AbdulAjadi1/FPGA-Board/documentation/critical_length.png

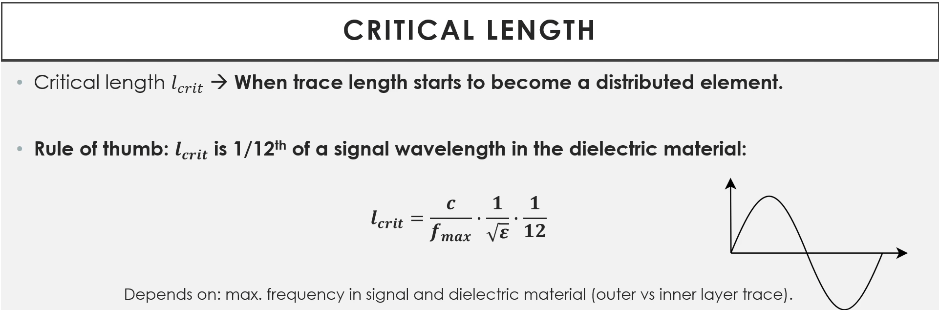
documentation/critical_length.png
