AbdulAjadi1/FPGA-Board/documentation/ddr3.png

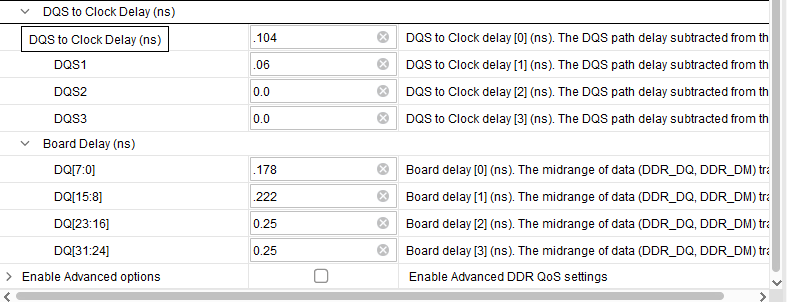
documentation/ddr3.png
