AbdulAjadi1/FPGA-Board/documentation/microstrip_stripline_delay.png

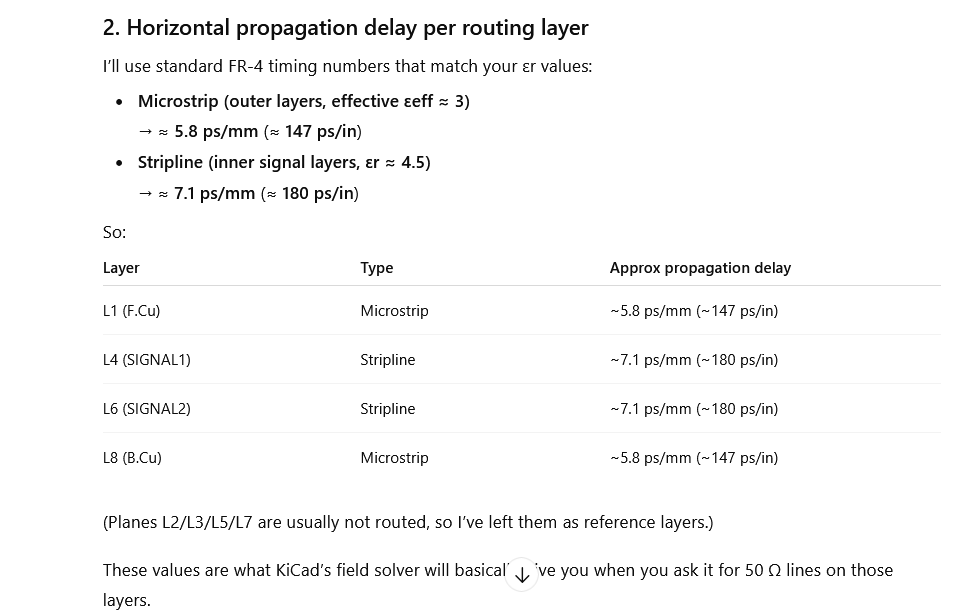
documentation/microstrip_stripline_delay.png
