AbdulAjadi1/FPGA-Board/3dmodels/ECS-2520MV-120-BN-TR.step

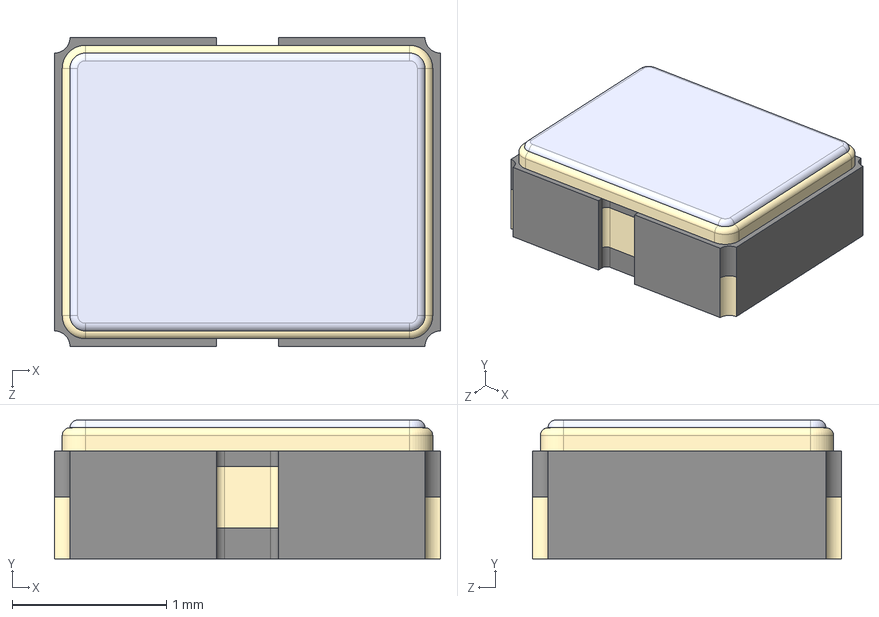
[picture p25: CAD file, 2025-12-17]
3dmodels/ECS-2520MV-120-BN-TR.step
2.50 x 0.9 x 2.00 mm
