AbdulAjadi1/FPGA-Board/3dmodels/cg0402mlu.stp

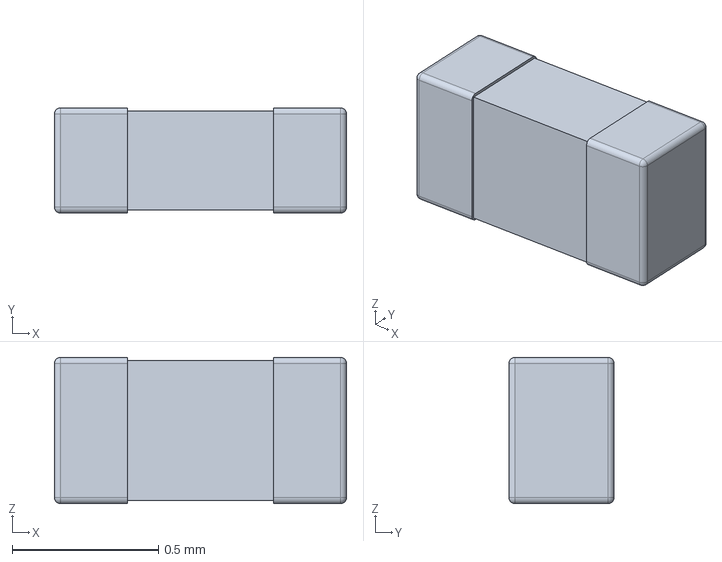
[picture p26: CAD file, 2025-12-17]
3dmodels/cg0402mlu.stp
1.00 x 0.36 x 0.5 mm
