AbdulAjadi1/FPGA-Board/3dmodels/DCU0008A.stp

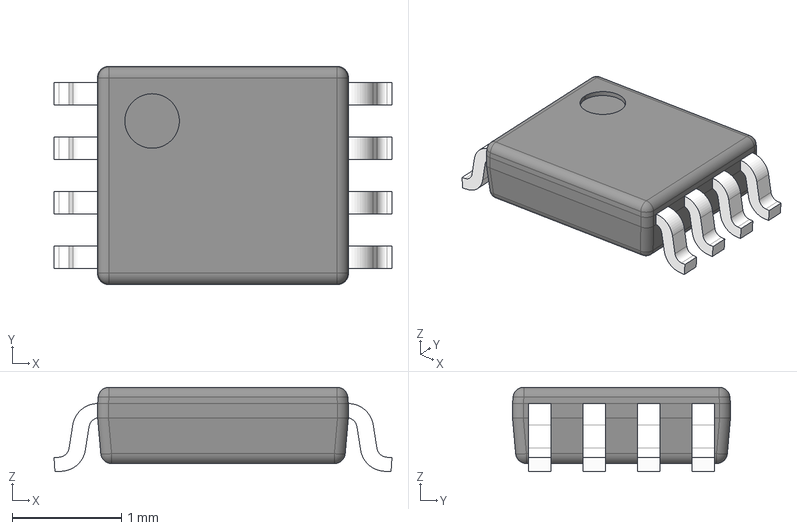
[picture p28: CAD file, 2025-11-05]
3dmodels/DCU0008A.stp
3.10 x 2.00 x 0.775 mm
BODY-VSSOP
LEAD-VSSOP x 8
