AbdulAjadi1/FPGA-Board/3dmodels/R_0201_0603Metric.step

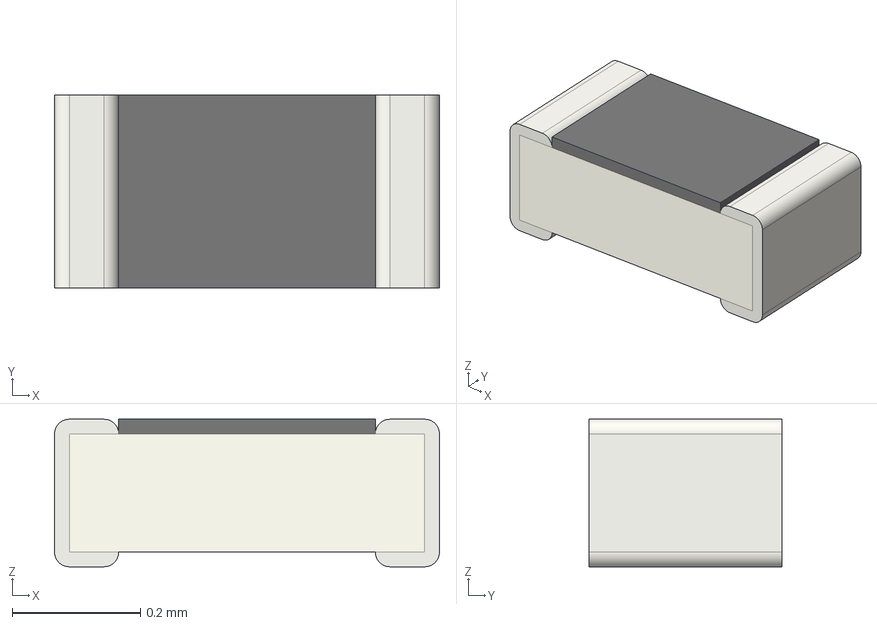
[picture p29: CAD file, 2025-11-05]
3dmodels/R_0201_0603Metric.step
0.6 x 0.3 x 0.23 mm
