AbdulAjadi1/FPGA-Board/3dmodels/UE27AC54100.step

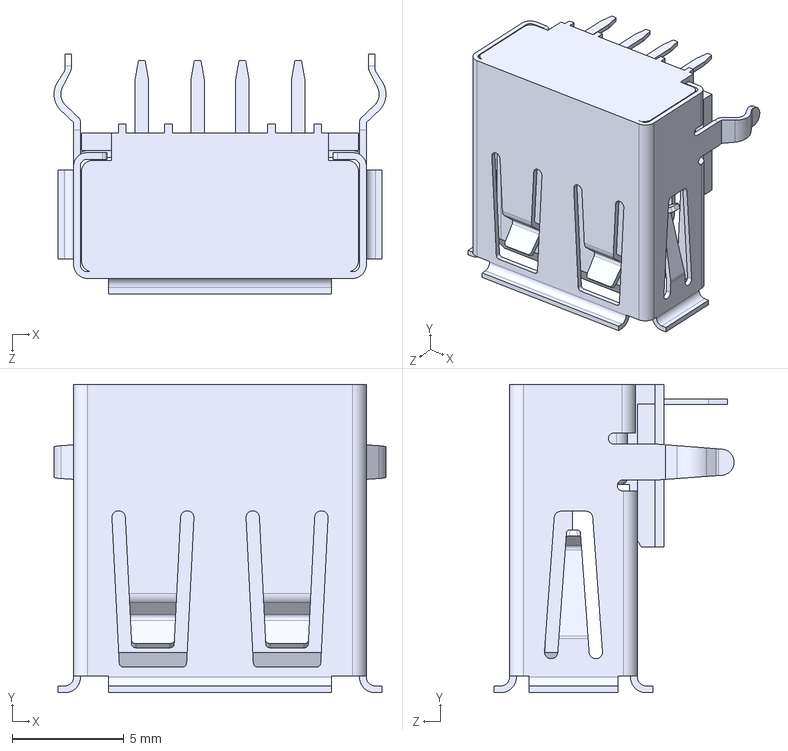
[picture p31: CAD file, 2025-09-09]
3dmodels/UE27AC54100.step
14.9 x 13.8 x 10.7 mm
