AbdulAjadi1/FPGA-Board/3dmodels/PJ-102AH.STEP

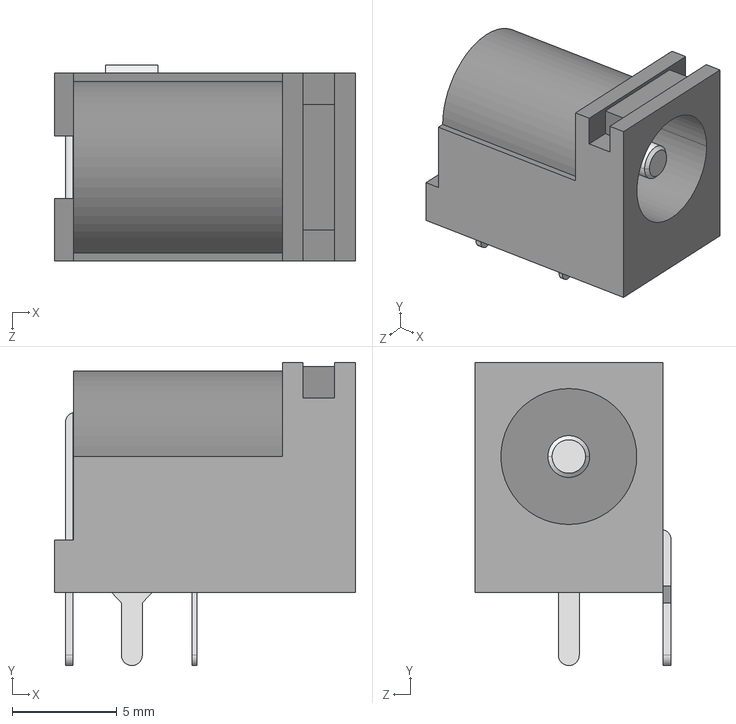
[picture p32: CAD file, 2025-09-09]
3dmodels/PJ-102AH.STEP
14.4 x 14.5 x 9.40 mm
