AbdulAjadi1/FPGA-Board/3dmodels/CR_050R3C2P_AVX.step

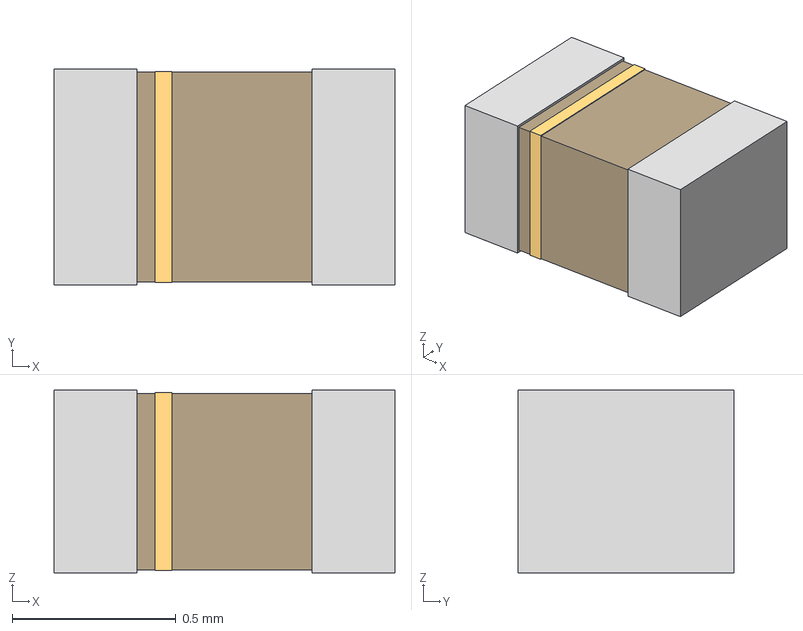
[picture p33: CAD file, 2025-09-09]
3dmodels/CR_050R3C2P_AVX.step
1.04 x 0.66 x 0.559 mm
