AbdulAjadi1/FPGA-Board/3dmodels/SJ1-3525NG.STEP

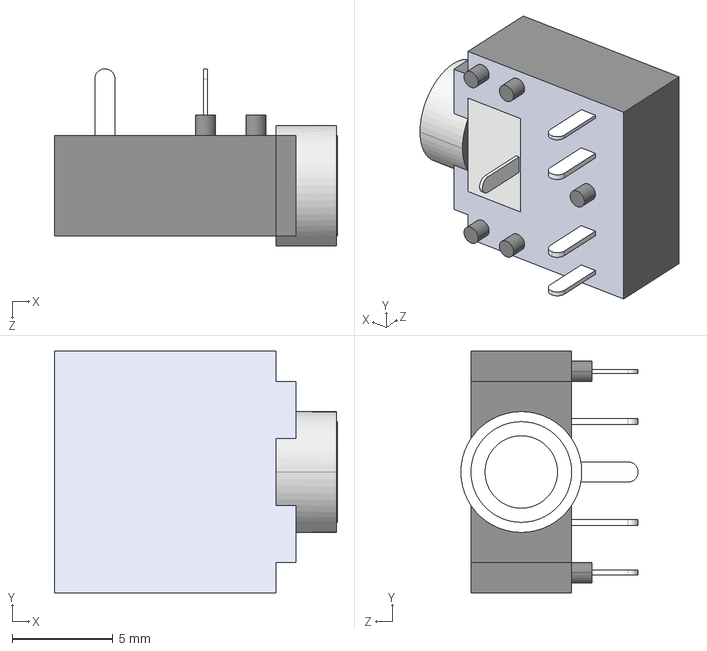
[picture p34: CAD file, 2025-09-09]
3dmodels/SJ1-3525NG.STEP
14.0 x 12.0 x 8.80 mm
