AbdulAjadi1/FPGA-Board/3dmodels/RM_10_ADI.step

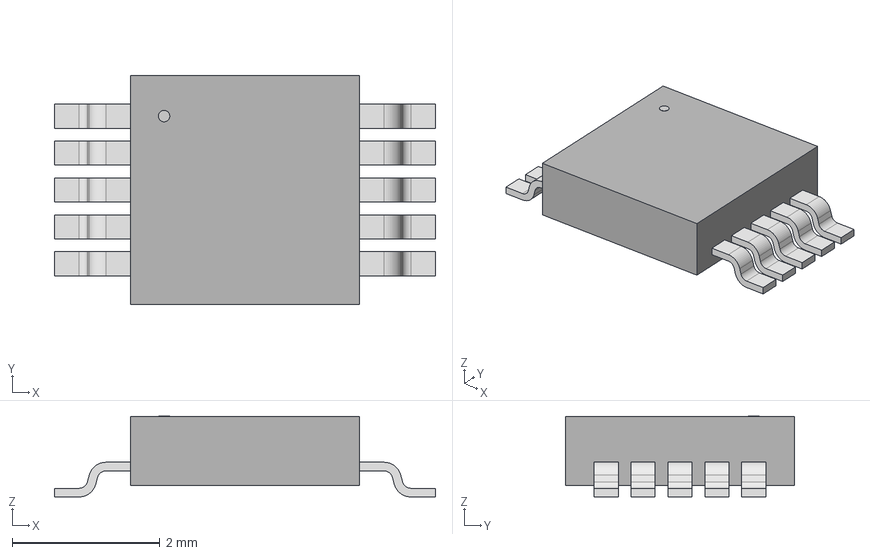
[picture p35: CAD file, 2025-09-09]
3dmodels/RM_10_ADI.step
5.16 x 3.10 x 1.09 mm
