AbdulAjadi1/FPGA-Board/3dmodels/TSX-322526_0000MF09Z-AC3_EPS.step

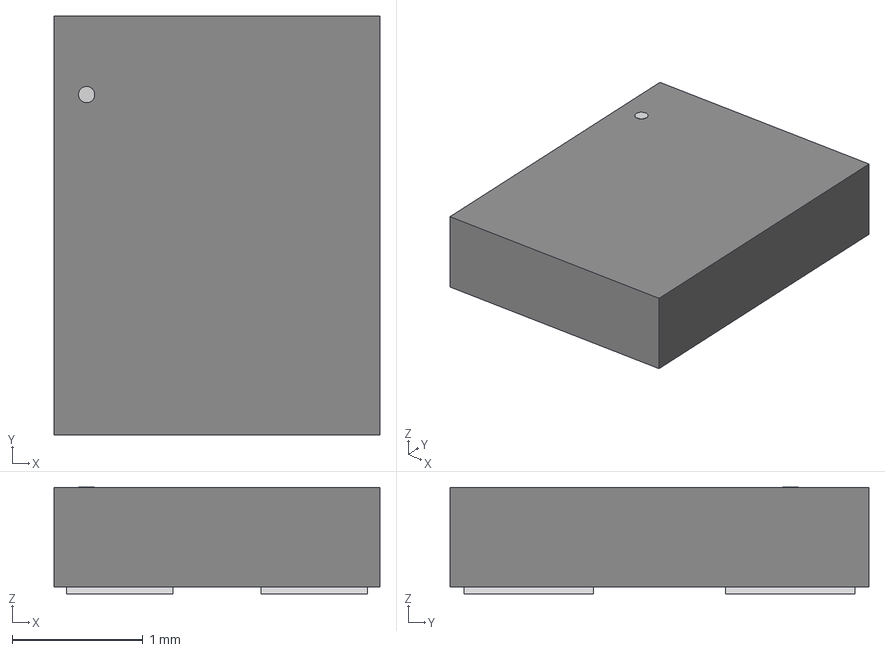
[picture p36: CAD file, 2025-09-09]
3dmodels/TSX-322526_0000MF09Z-AC3_EPS.step
2.49 x 3.20 x 0.815 mm
