AbdulAjadi1/FPGA-Board/3dmodels/NR5040T2R2N.STEP

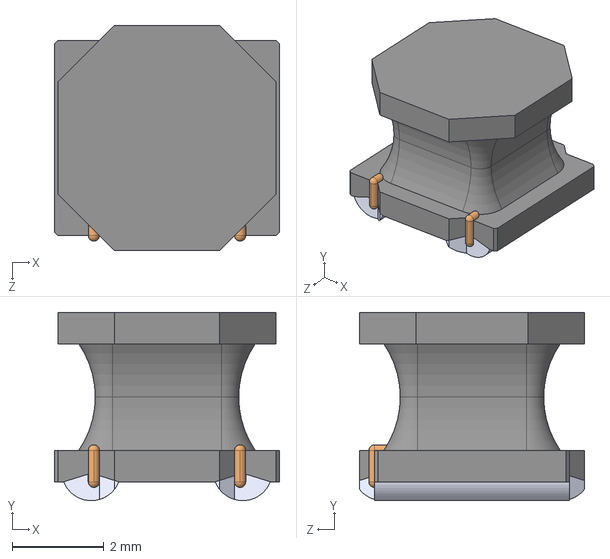
[picture p38: CAD file, 2025-09-09]
3dmodels/NR5040T2R2N.STEP
4.90 x 4.10 x 4.90 mm
