AbdulAjadi1/FPGA-Board/3dmodels/BAS16XV2T1G.step

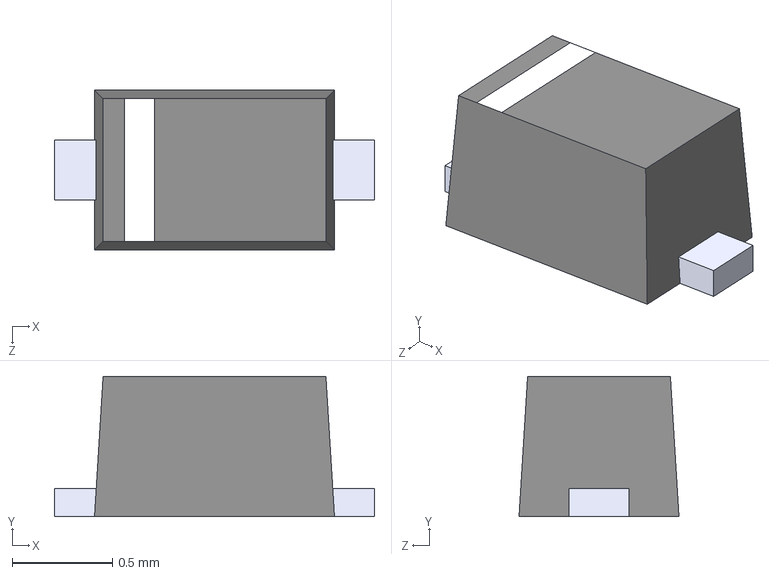
[picture p40: CAD file, 2025-09-09]
3dmodels/BAS16XV2T1G.step
1.60 x 0.7 x 0.8 mm
