AbdulAjadi1/FPGA-Board/3dmodels/DBV0006A.stp

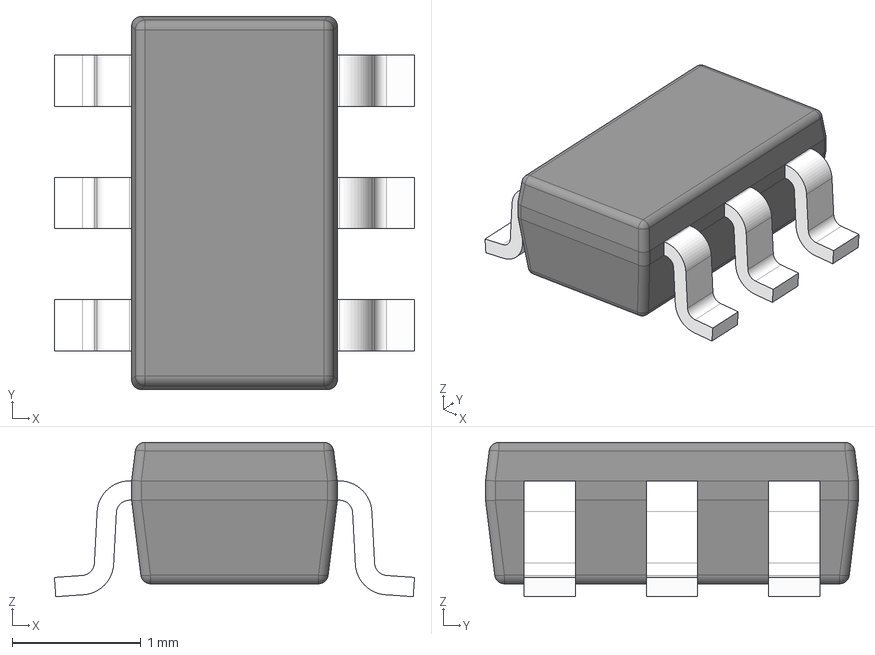
[picture p41: CAD file, 2025-09-09]
3dmodels/DBV0006A.stp
2.80 x 2.90 x 1.20 mm
BODY-SOT
LEAD-SOT x 6
