AbdulAjadi1/FPGA-Board/3dmodels/EG1218.step

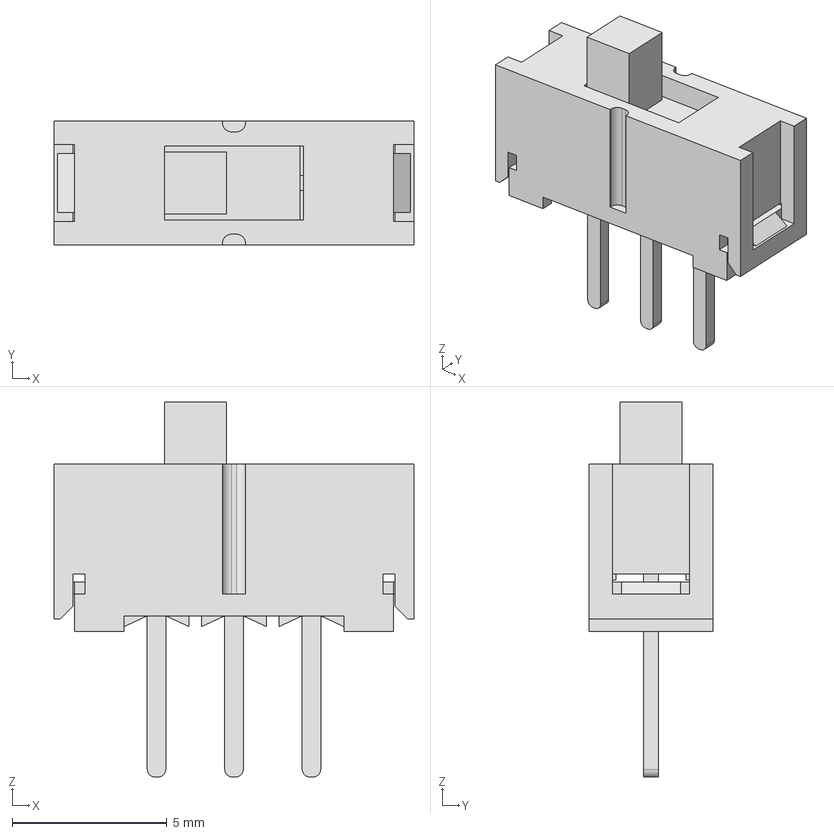
[picture p42: CAD file, 2025-09-09]
3dmodels/EG1218.step
11.6 x 4.00 x 12.1 mm
