AbdulAjadi1/FPGA-Board/3dmodels/c-5787834-1-c-3d.stp

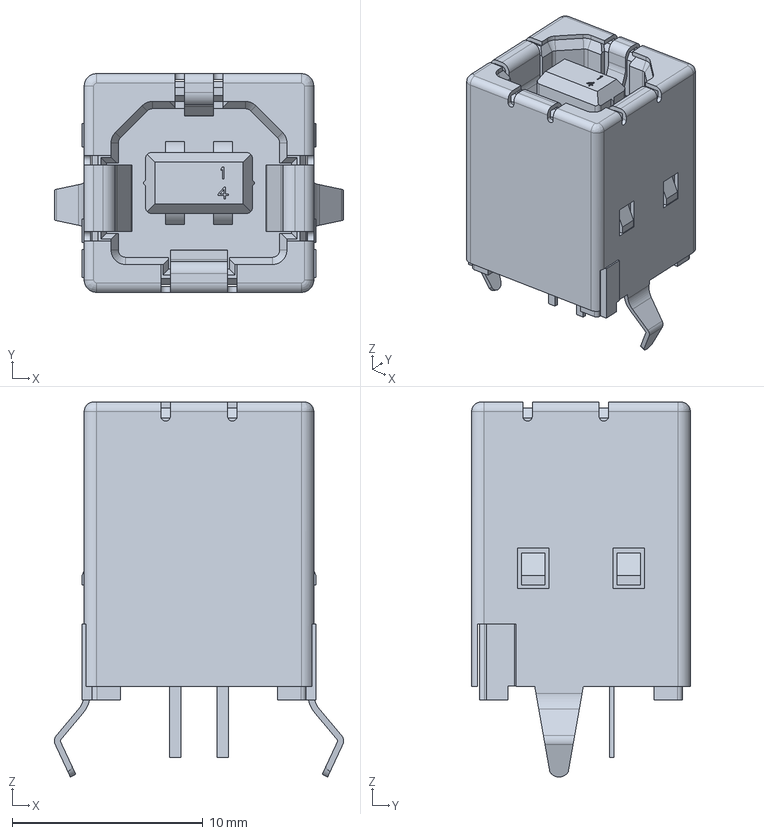
[picture p43: CAD file, 2025-09-09]
3dmodels/c-5787834-1-c-3d.stp
15.1 x 11.5 x 19.6 mm
