AbdulAjadi1/FPGA-Board/3dmodels/IND_TYS60282_LRD.step

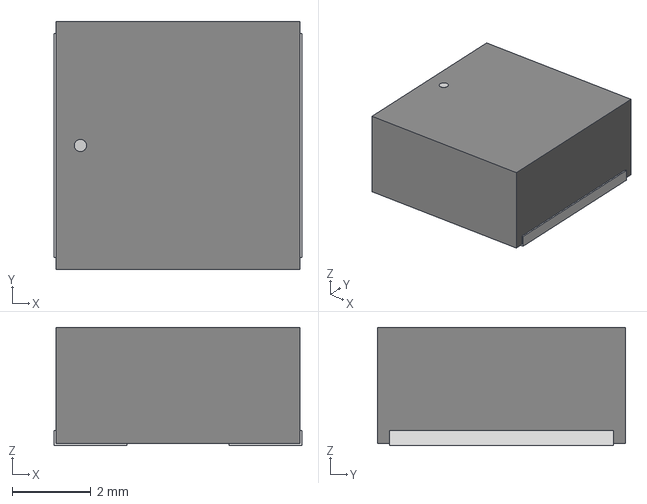
[picture p44: CAD file, 2025-09-09]
3dmodels/IND_TYS60282_LRD.step
6.30 x 6.30 x 3.00 mm
