AbdulAjadi1/FPGA-Board/3dmodels/USB-A-S-F-B-SM2.stp

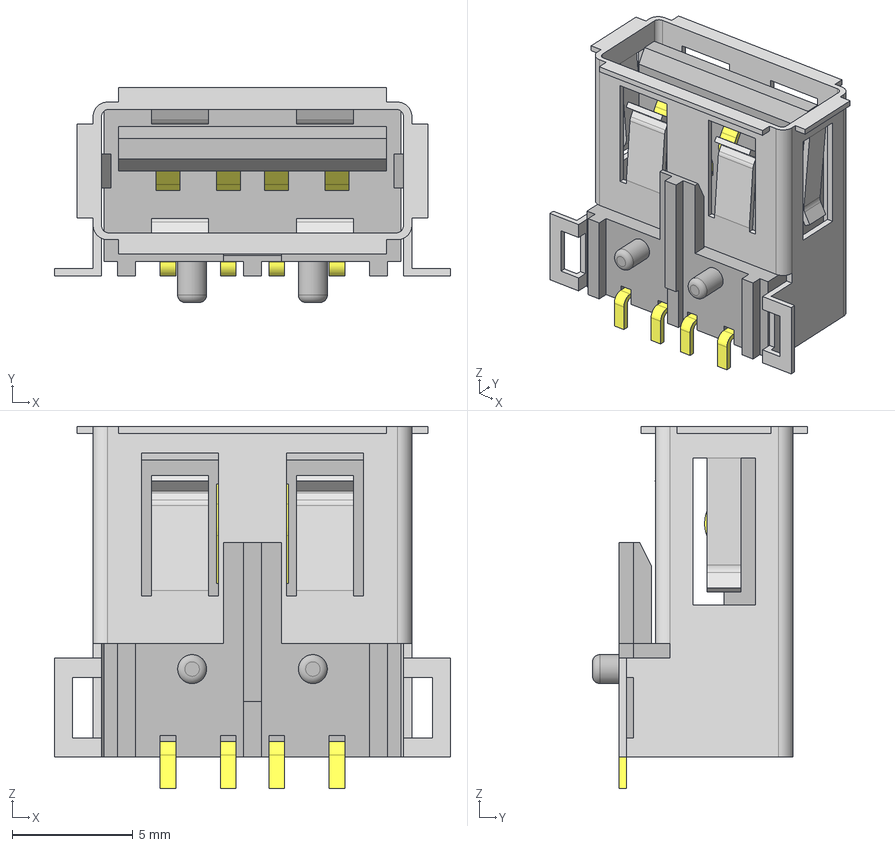
[picture p45: CAD file, 2025-09-09]
3dmodels/USB-A-S-F-B-SM2.stp
16.4 x 8.90 x 15.0 mm
USB-A-S-SM2_S
USB-A-S-B-SM2_B
USB-A-S-SM2_P
