AbdulAjadi1/FPGA-Board/3dmodels/BSS214NH6327XTSA1.stp

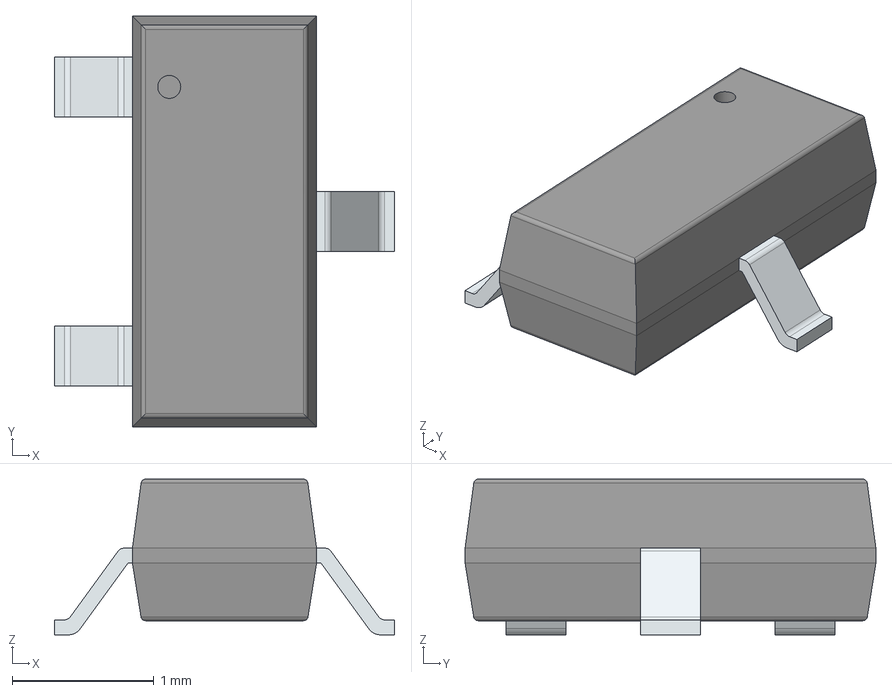
[picture p46: CAD file, 2025-09-09]
3dmodels/BSS214NH6327XTSA1.stp
2.40 x 2.90 x 1.10 mm
PinsArrayL
FilletPinR
