AbdulAjadi1/FPGA-Board/3dmodels/SO3016_INF.step

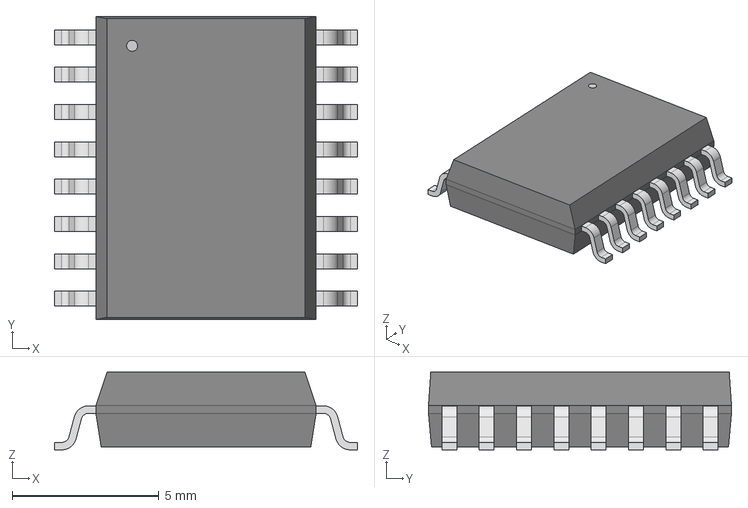
[picture p47: CAD file, 2025-09-09]
3dmodels/SO3016_INF.step
10.3 x 10.3 x 2.64 mm
