AbdulAjadi1/FPGA-Board/3dmodels/LED_0402_1005Metric.step

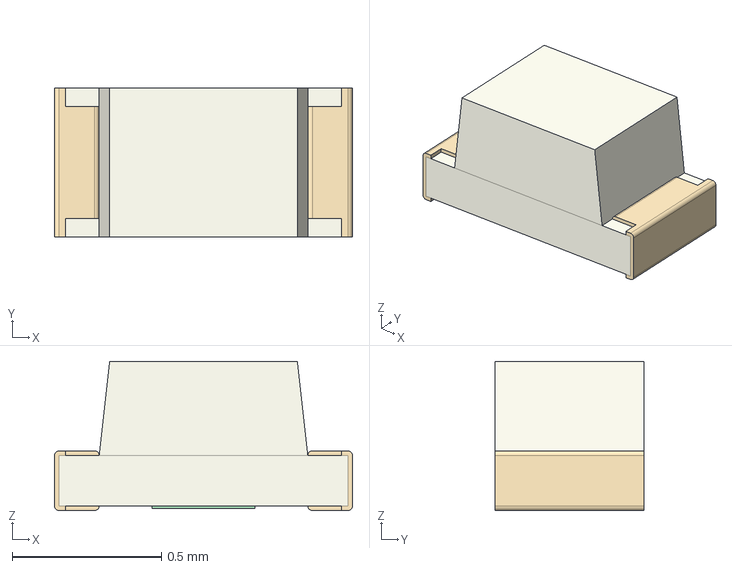
[picture p48: CAD file, 2025-09-09]
3dmodels/LED_0402_1005Metric.step
1.00 x 0.5 x 0.5 mm
