AbdulAjadi1/FPGA-Board/3dmodels/NL17SZ17XV5T2G.STEP

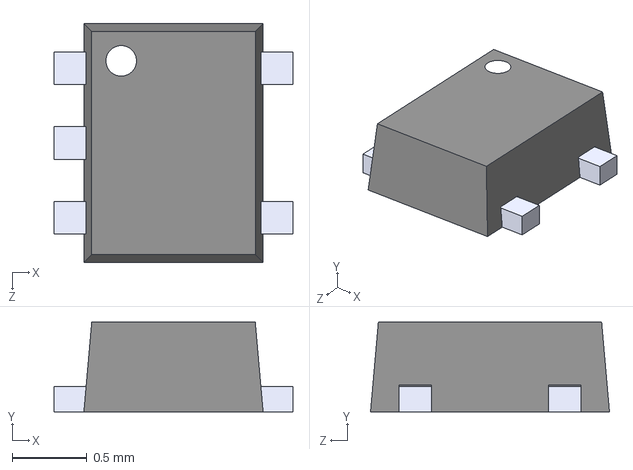
[picture p49: CAD file, 2025-09-09]
3dmodels/NL17SZ17XV5T2G.STEP
1.60 x 0.6 x 1.60 mm
