AbdulAjadi1/FPGA-Board/3dmodels/LED_SMLV56_ROM.step

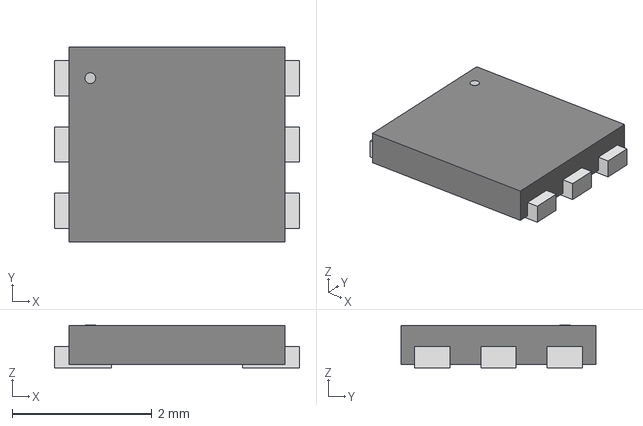
[picture p50: CAD file, 2025-09-09]
3dmodels/LED_SMLV56_ROM.step
3.51 x 2.79 x 0.612 mm
