AbdulAjadi1/FPGA-Board/3dmodels/IS43TR16256B-125KBLI.step

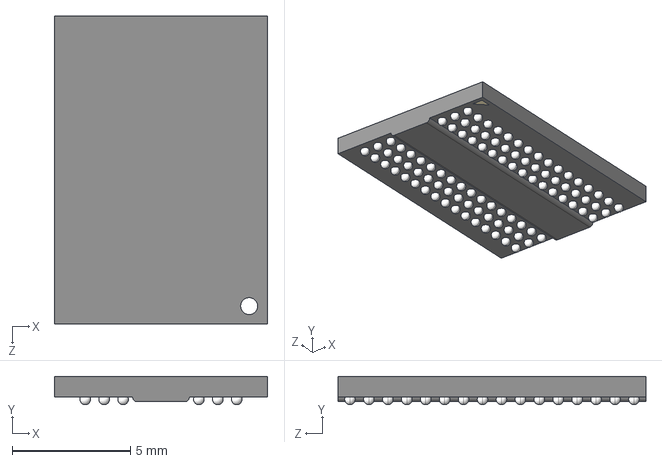
[picture p51: CAD file, 2025-09-09]
3dmodels/IS43TR16256B-125KBLI.step
9.00 x 1.20 x 13.0 mm
