AbdulAjadi1/FPGA-Board/3dmodels/DBZ0003A.stp

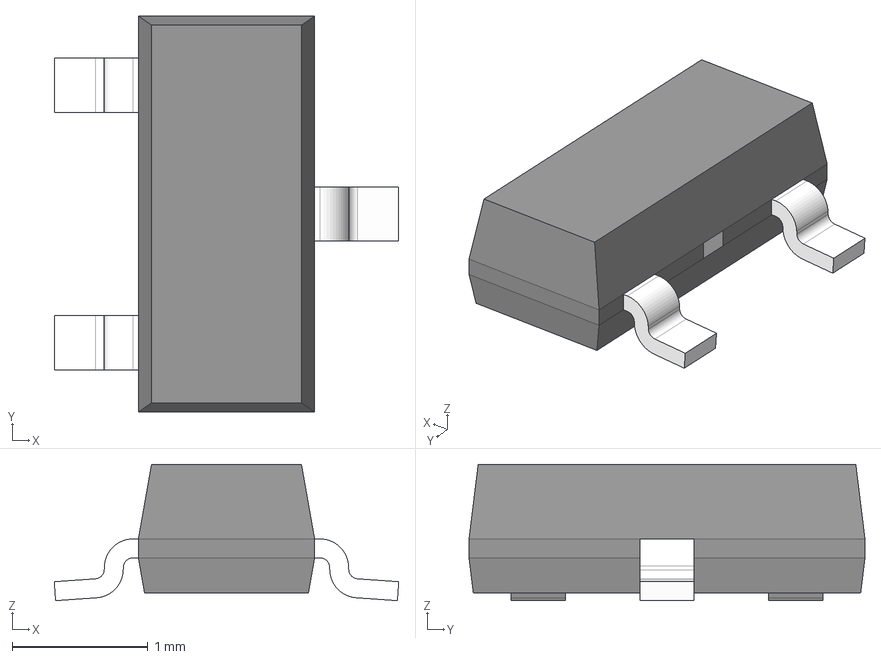
[picture p52: CAD file, 2025-09-09]
3dmodels/DBZ0003A.stp
2.54 x 2.92 x 1.01 mm
BODY-SOT
LEAD-SOT x 3
PIN1-ID
TIEBAR
