AbdulAjadi1/FPGA-Board/3dmodels/ABMM-25.000MHZ-B2-T.step

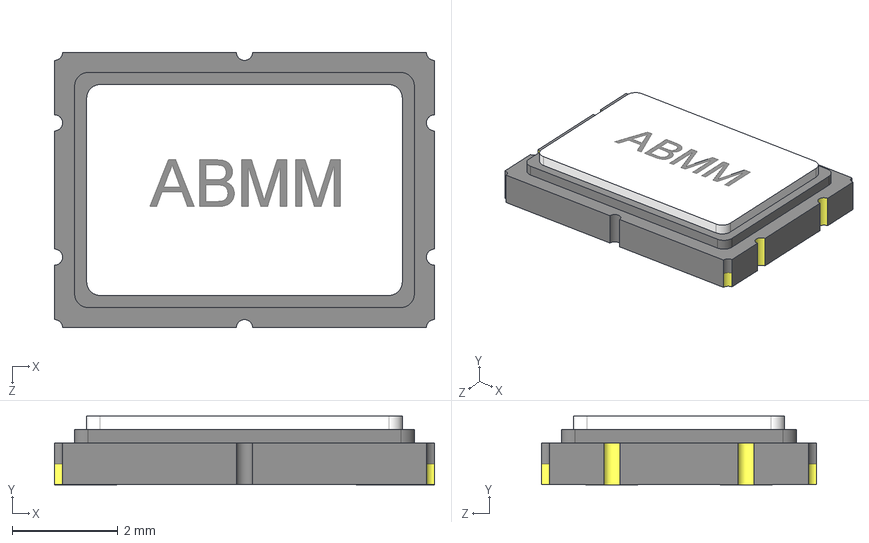
[picture p53: CAD file, 2025-09-09]
3dmodels/ABMM-25.000MHZ-B2-T.step
7.19 x 1.30 x 5.21 mm
