AbdulAjadi1/FPGA-Board/3dmodels/PinHeader_1x02_P2.54mm_Vertical.step

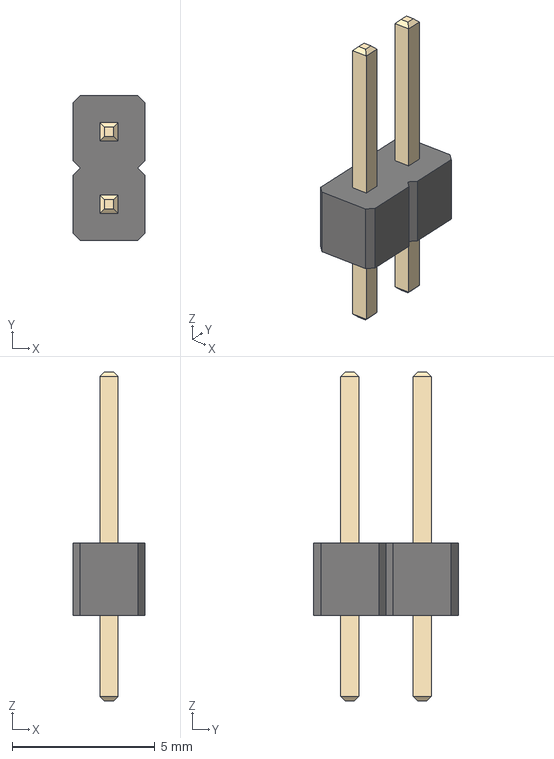
[picture p54: CAD file, 2025-09-09]
3dmodels/PinHeader_1x02_P2.54mm_Vertical.step
2.54 x 5.08 x 11.5 mm
