AbdulAjadi1/FPGA-Board/3dmodels/PinHeader_1x05_P2.54mm_Vertical.step

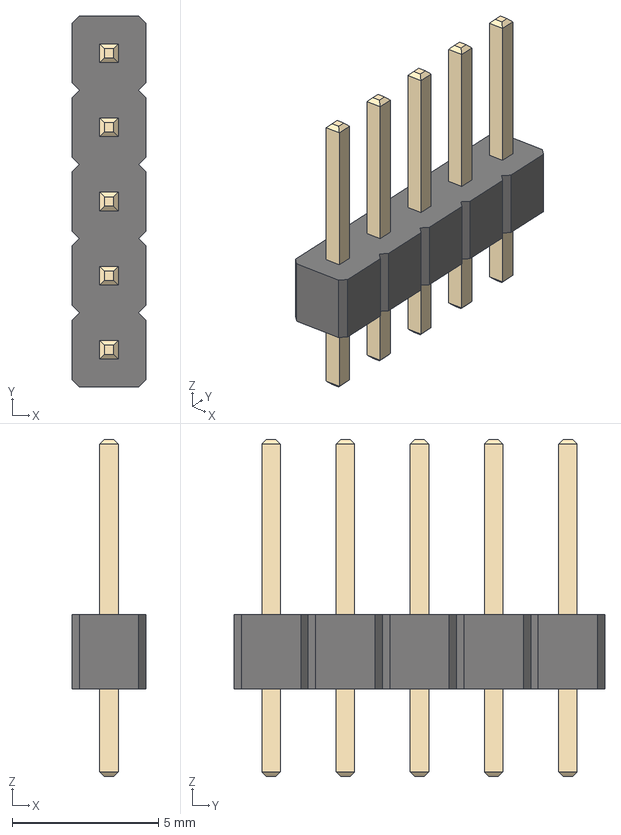
[picture p55: CAD file, 2025-09-09]
3dmodels/PinHeader_1x05_P2.54mm_Vertical.step
2.54 x 12.7 x 11.5 mm
