AbdulAjadi1/FPGA-Board/3dmodels/L_0402.step

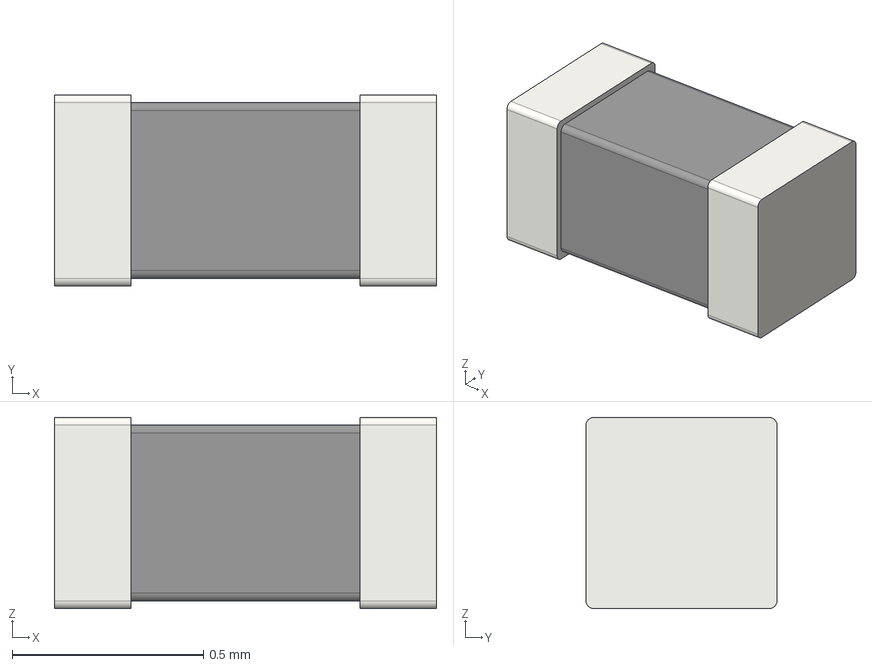
[picture p56: CAD file, 2025-09-09]
3dmodels/L_0402.step
1.00 x 0.5 x 0.5 mm
