AbdulAjadi1/FPGA-Board/3dmodels/64QFN_FT2232HQ_FTD.step

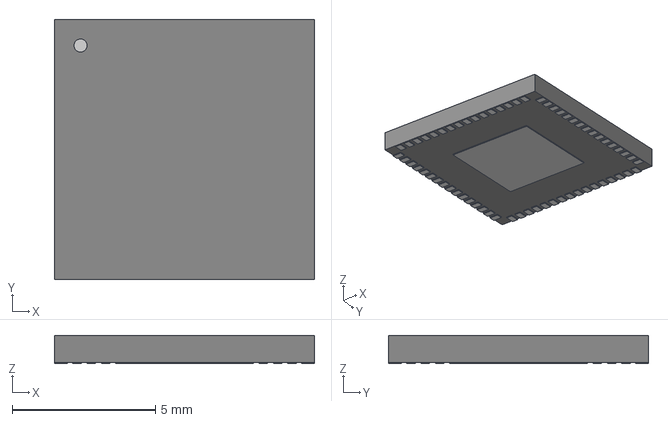
[picture p57: CAD file, 2025-09-09]
3dmodels/64QFN_FT2232HQ_FTD.step
9.07 x 9.07 x 0.993 mm
