AbdulAjadi1/FPGA-Board/3dmodels/HFJ11-1G01ERL.stp

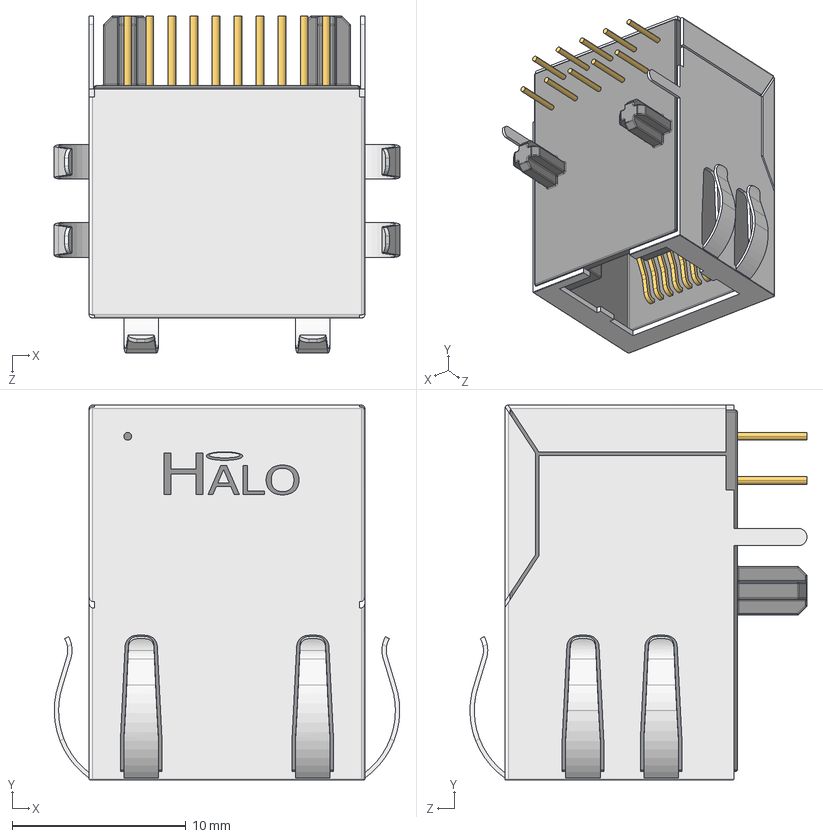
[picture p58: CAD file, 2025-09-09]
3dmodels/HFJ11-1G01ERL.stp
19.9 x 21.6 x 19.4 mm
housing
pins
plastic
logo_
