AbdulAjadi1/FPGA-Board/3dmodels/QFN4_5X3P2_MCH.step

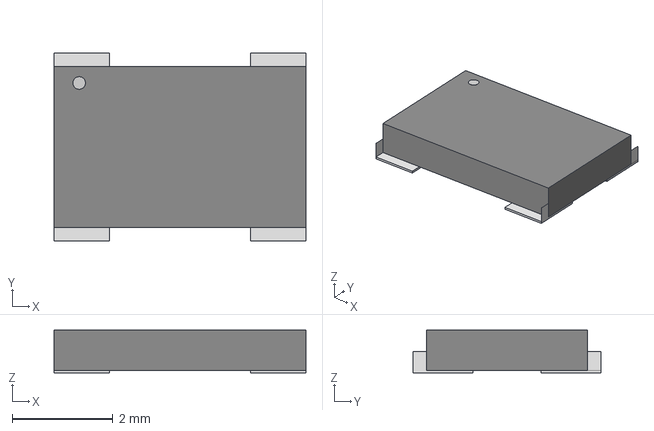
[picture p59: CAD file, 2025-09-09]
3dmodels/QFN4_5X3P2_MCH.step
5.00 x 3.74 x 0.853 mm
