AbdulAjadi1/FPGA-Board/3dmodels/IND_BOURNS_SRN4018.step

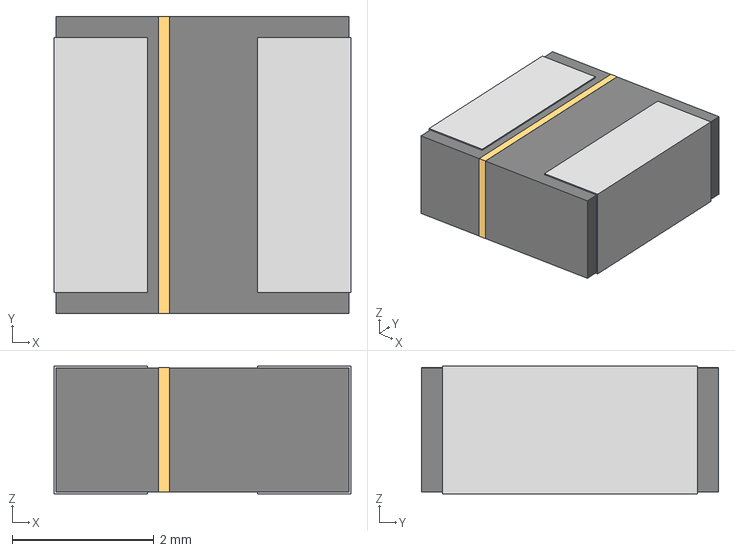
[picture p60: CAD file, 2025-09-09]
3dmodels/IND_BOURNS_SRN4018.step
4.19 x 4.20 x 1.80 mm
