AbdulAjadi1/FPGA-Board/3dmodels/SG-8018CE_50.0000M-TJHPA.step

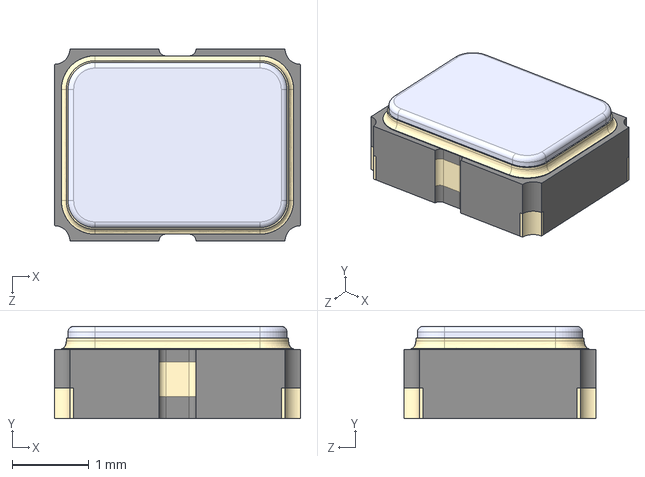
[picture p61: CAD file, 2025-09-09]
3dmodels/SG-8018CE_50.0000M-TJHPA.step
3.20 x 1.20 x 2.50 mm
