AbdulAjadi1/FPGA-Board/3dmodels/SMBJ15CA-E3_52.stp

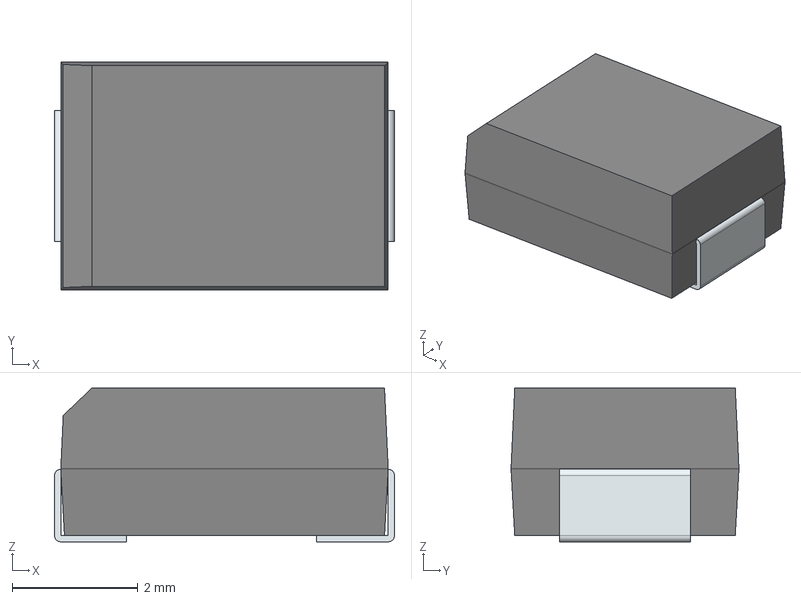
[picture p62: CAD file, 2025-09-09]
3dmodels/SMBJ15CA-E3_52.stp
5.40 x 3.62 x 2.44 mm
FilletPin1
FilletPin2
