AbdulAjadi1/FPGA-Board/3dmodels/SOT-23-5_MC_MCH.step

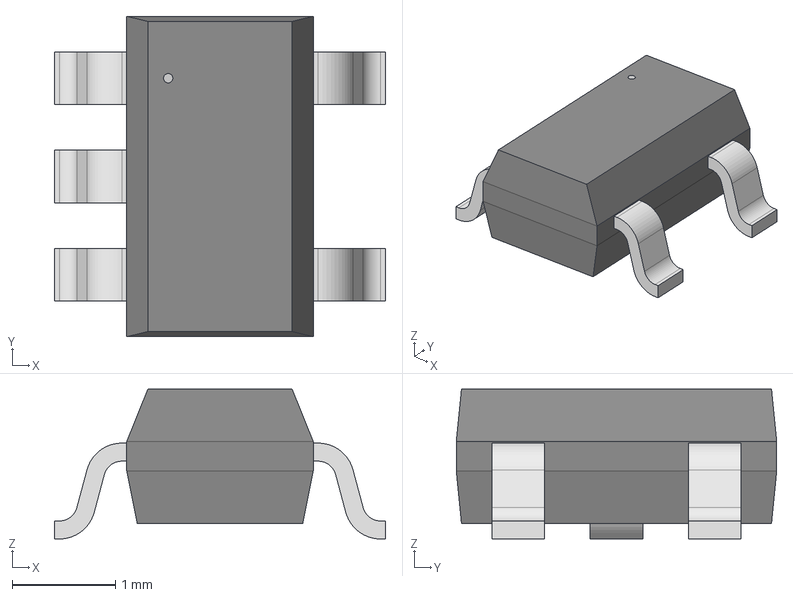
[picture p63: CAD file, 2025-09-09]
3dmodels/SOT-23-5_MC_MCH.step
3.20 x 3.10 x 1.45 mm
