AbdulAjadi1/FPGA-Board/3dmodels/IND_SRP4020_BRN.step

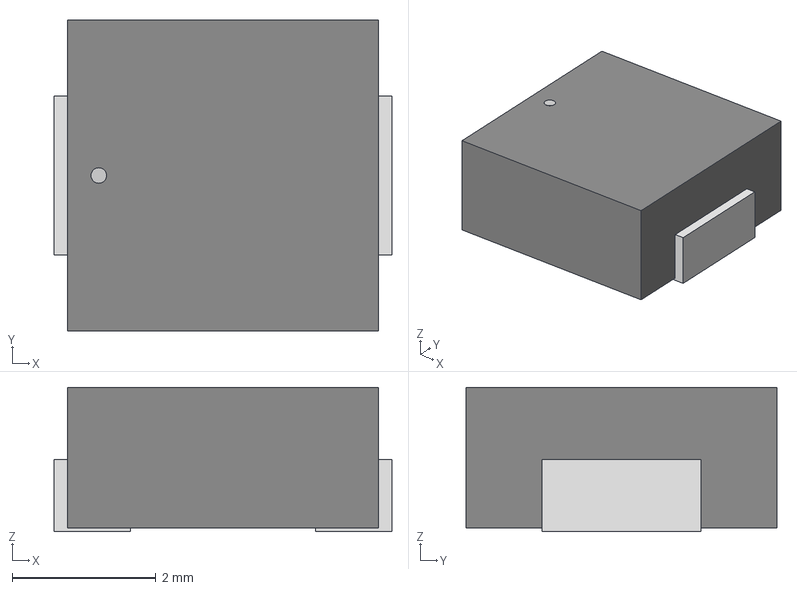
[picture p64: CAD file, 2025-09-09]
3dmodels/IND_SRP4020_BRN.step
4.70 x 4.32 x 2.01 mm
