AbdulAjadi1/FPGA-Board/3dmodels/USC-ZKN_r.stp

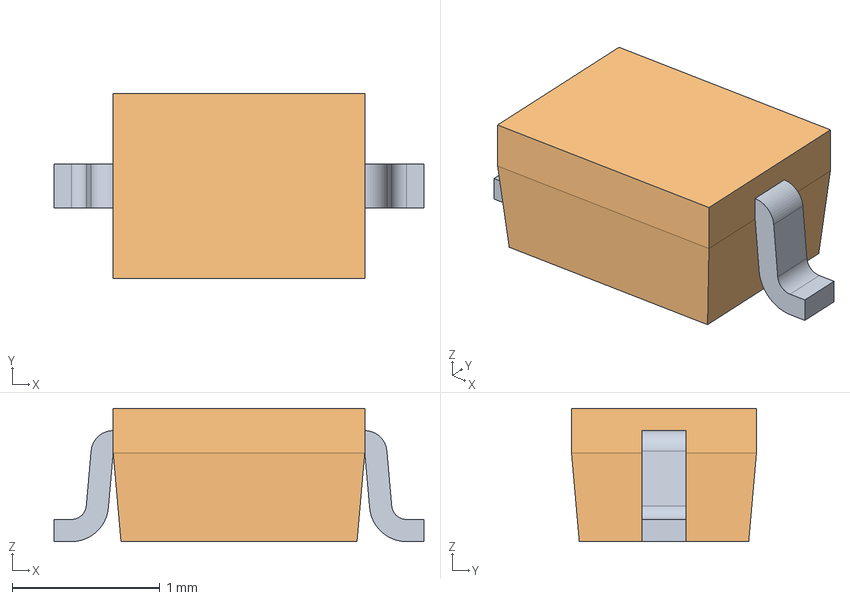
[picture p65: CAD file, 2025-09-09]
3dmodels/USC-ZKN_r.stp
2.50 x 1.25 x 0.9 mm
