AbdulAjadi1/FPGA-Board/3dmodels/PRT-14017.STEP

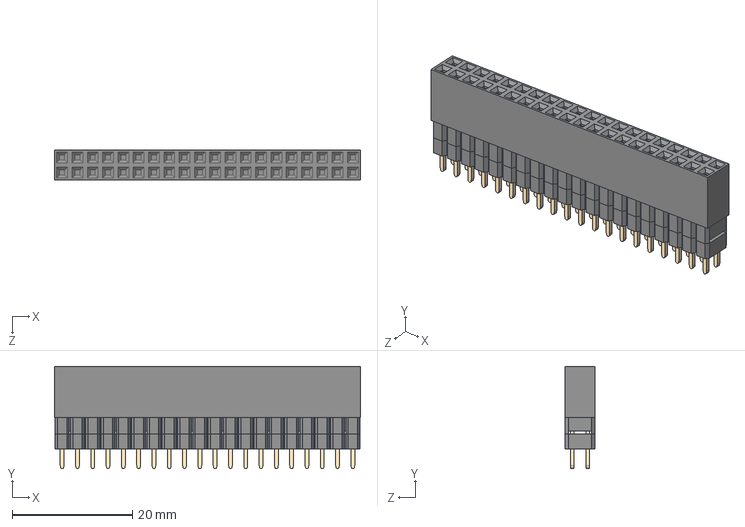
[picture p67: CAD file, 2025-09-09]
3dmodels/PRT-14017.STEP
50.8 x 17.0 x 5.00 mm
