AbdulAjadi1/FPGA-Board/3dmodels/ZDO_SOD123_DIO.step

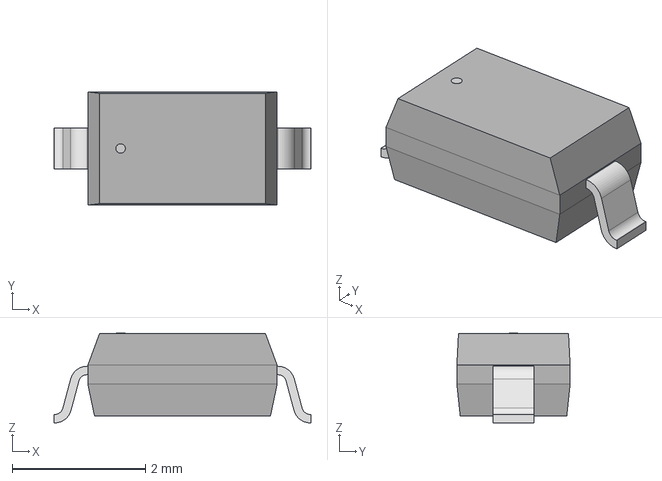
[picture p68: CAD file, 2025-09-09]
3dmodels/ZDO_SOD123_DIO.step
3.86 x 1.70 x 1.35 mm
