AbdulAjadi1/FPGA-Board/3dmodels/US8-8_2P1X2P4_ONS.step

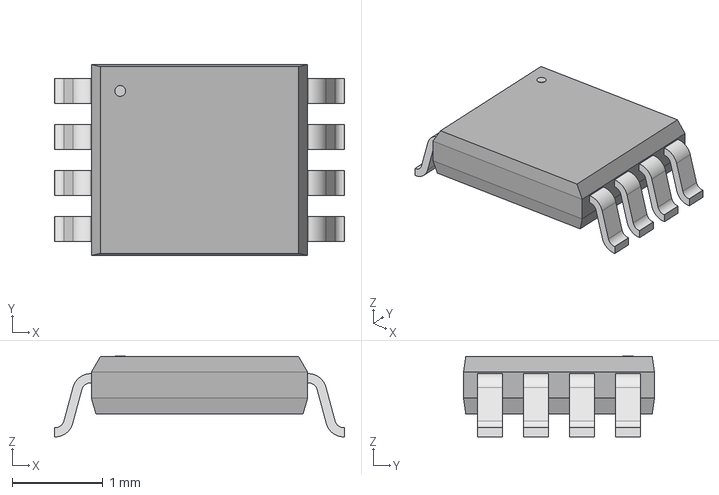
[picture p69: CAD file, 2025-09-09]
3dmodels/US8-8_2P1X2P4_ONS.step
3.20 x 2.11 x 0.892 mm
