AbdulAjadi1/FPGA-Board/3dmodels/PTS645SK50SMTR92 LFS.STEP

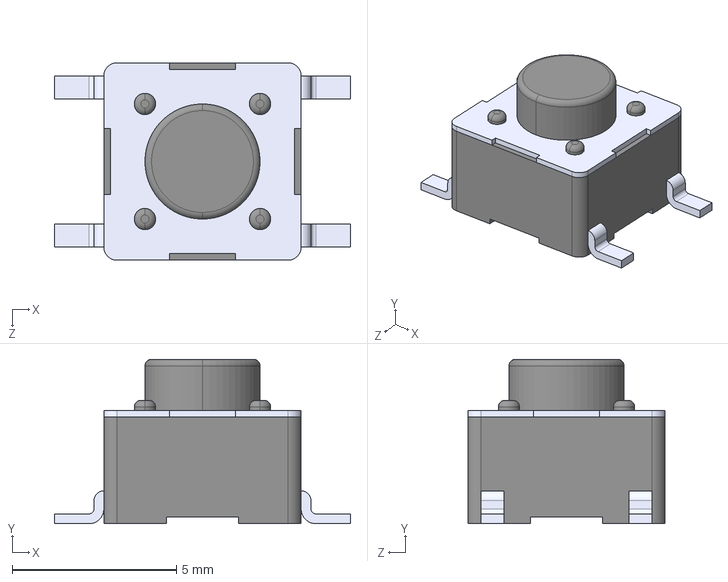
[picture p70: CAD file, 2025-09-09]
3dmodels/PTS645SK50SMTR92 LFS.STEP
9.00 x 5.00 x 6.00 mm
