AbdulAjadi1/FPGA-Board/3dmodels/TORX1950A_F_.stp

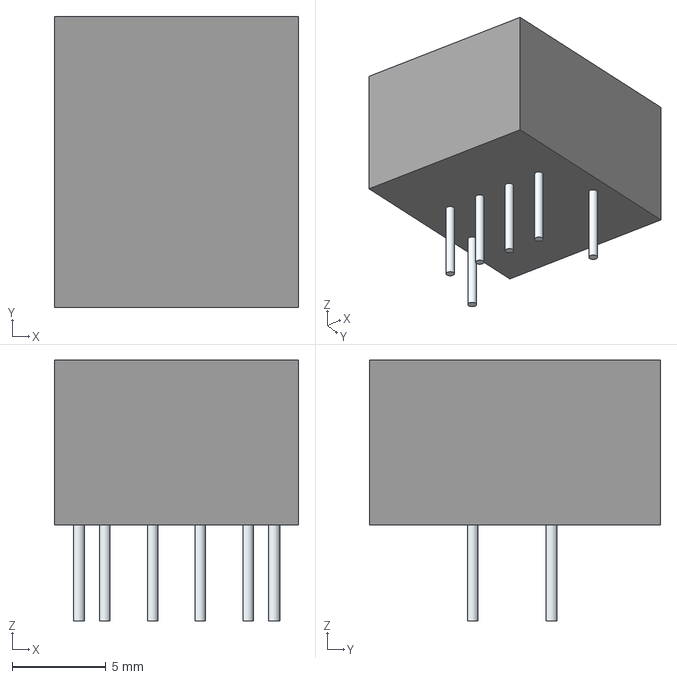
[picture p71: CAD file, 2025-09-09]
3dmodels/TORX1950A_F_.stp
13.0 x 15.5 x 13.9 mm
Leads
