AbdulAjadi1/FPGA-Board/3dmodels/C_1808_4520Metric.step

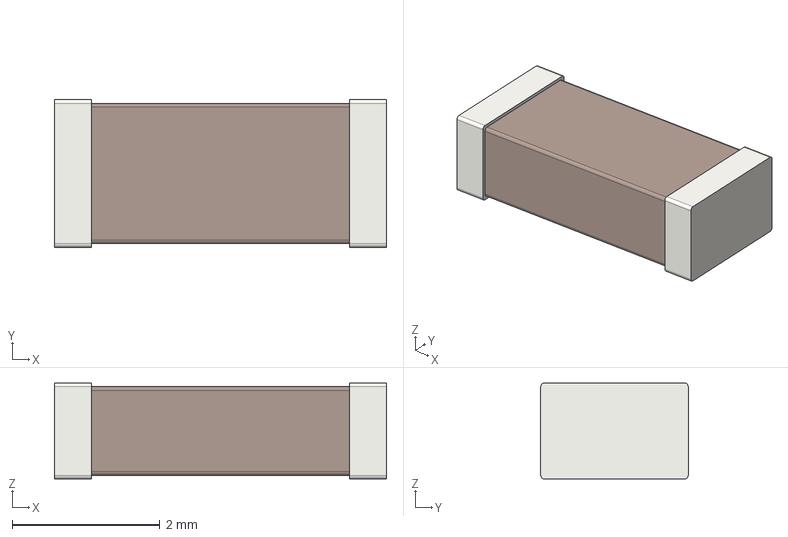
[picture p72: CAD file, 2025-09-09]
3dmodels/C_1808_4520Metric.step
4.50 x 2.00 x 1.30 mm
