AbdulAjadi1/FPGA-Board/3dmodels/RTW0024B.stp

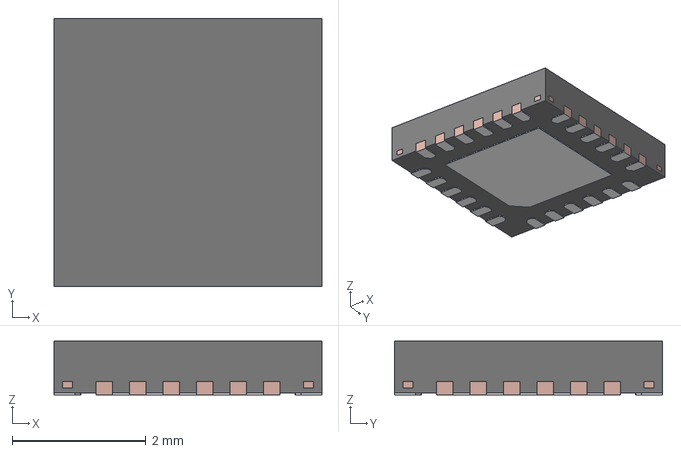
[picture p74: CAD file, 2025-09-09]
3dmodels/RTW0024B.stp
4.00 x 4.00 x 0.8 mm
FRAME
