AbdulAjadi1/FPGA-Board/3dmodels/TPS2051BDBVR.step

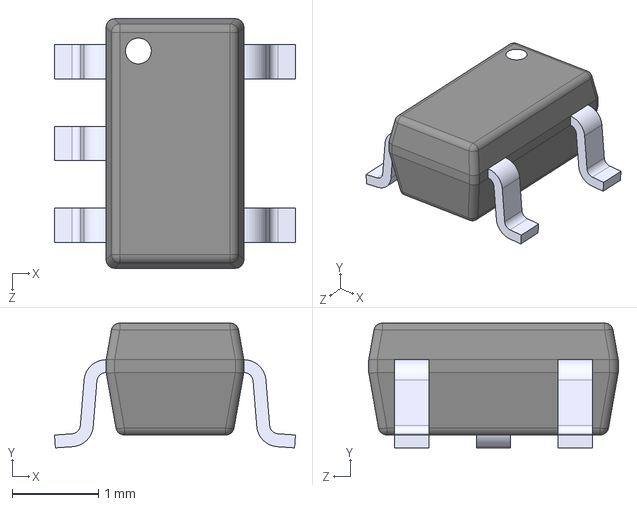
[picture p75: CAD file, 2025-09-09]
3dmodels/TPS2051BDBVR.step
2.80 x 1.45 x 2.90 mm
