AbdulAjadi1/FPGA-Board/3dmodels/CLG400_ZYNQ-7000_AMD.step

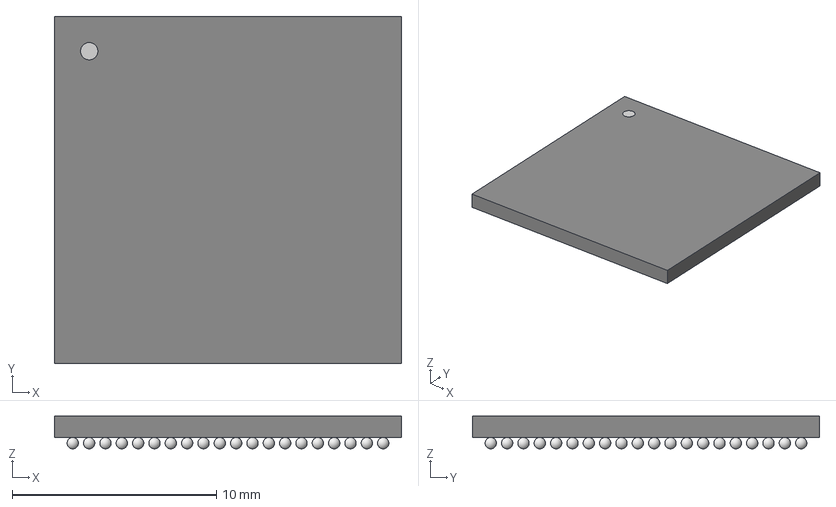
[picture p76: CAD file, 2025-09-09]
3dmodels/CLG400_ZYNQ-7000_AMD.step
17.0 x 17.0 x 1.60 mm
