AbdulAjadi1/FPGA-Board/3dmodels/TXS0102DCUR.step

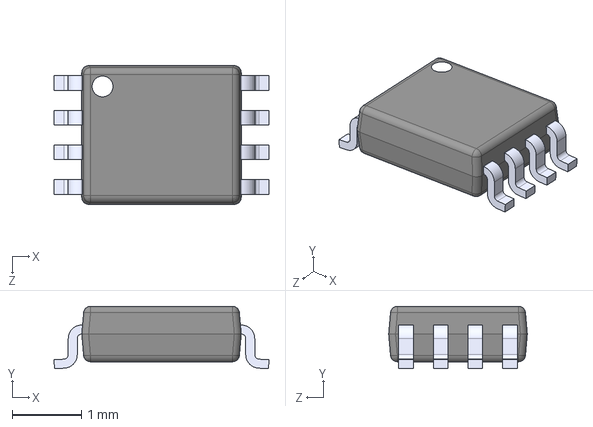
[picture p78: CAD file, 2025-09-09]
3dmodels/TXS0102DCUR.step
3.10 x 0.9 x 2.00 mm
