AbdulAjadi1/FPGA-Board/3dmodels/IND_SMDRI_SXN.step

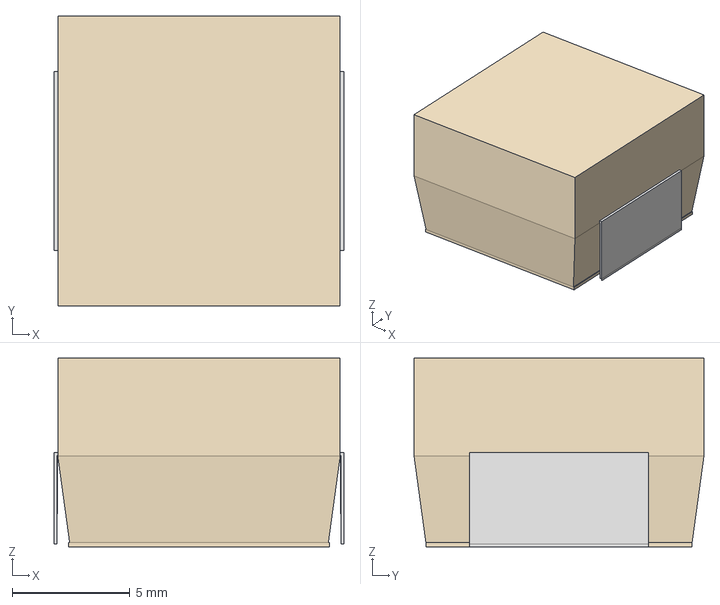
[picture p79: CAD file, 2025-09-09]
3dmodels/IND_SMDRI_SXN.step
12.3 x 12.3 x 8.00 mm
