AbdulAjadi1/FPGA-Board/3dmodels/RHB0032E.stp

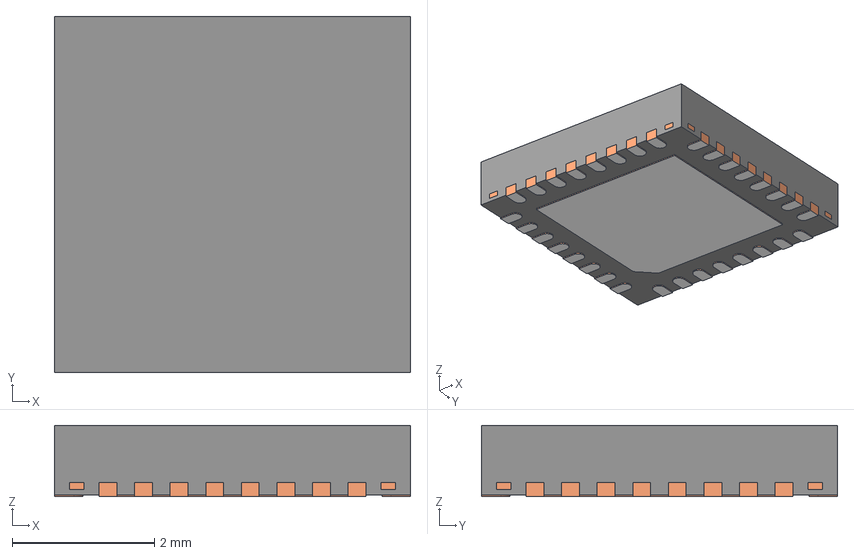
[picture p80: CAD file, 2025-09-09]
3dmodels/RHB0032E.stp
5.00 x 5.00 x 1.00 mm
BODY-QFN
FRAME-RHB0032E
PIN1-ID
