AbdulAjadi1/FPGA-Board/3dmodels/PinHeader_1x04_P2.54mm_Vertical.step

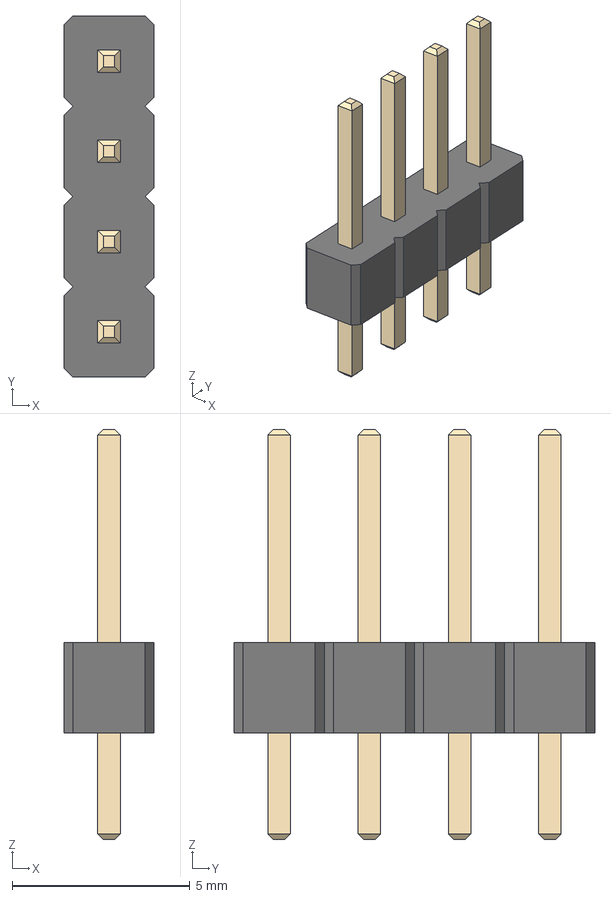
[picture p81: CAD file, 2025-09-09]
3dmodels/PinHeader_1x04_P2.54mm_Vertical.step
2.54 x 10.2 x 11.5 mm
