AbdulAjadi1/FPGA-Board/3dmodels/CRYSTAL_TXC_7M.step

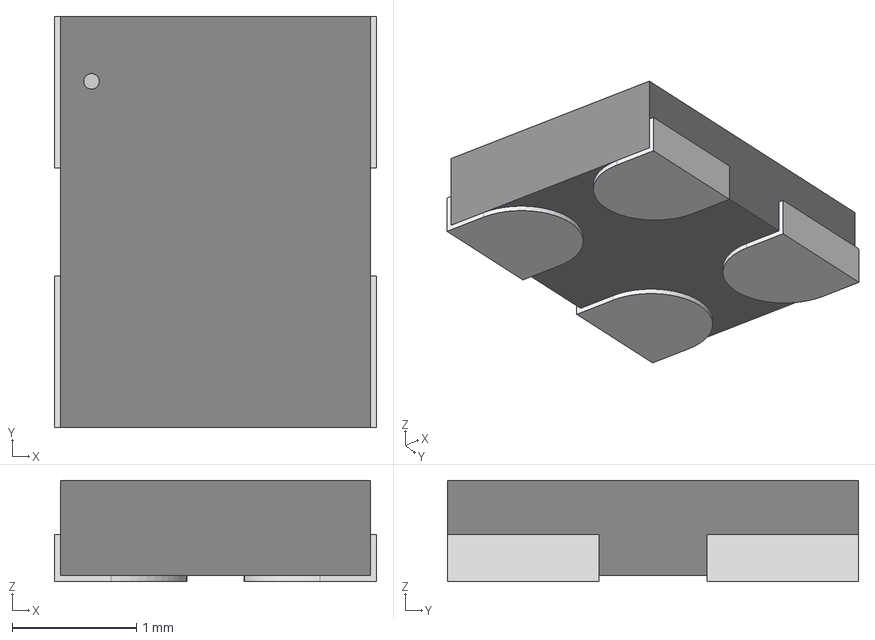
[picture p82: CAD file, 2025-09-09]
3dmodels/CRYSTAL_TXC_7M.step
2.59 x 3.30 x 0.815 mm
