AbdulAjadi1/FPGA-Board/3dmodels/SOIC8_4P9X3P9MC_MCH.step

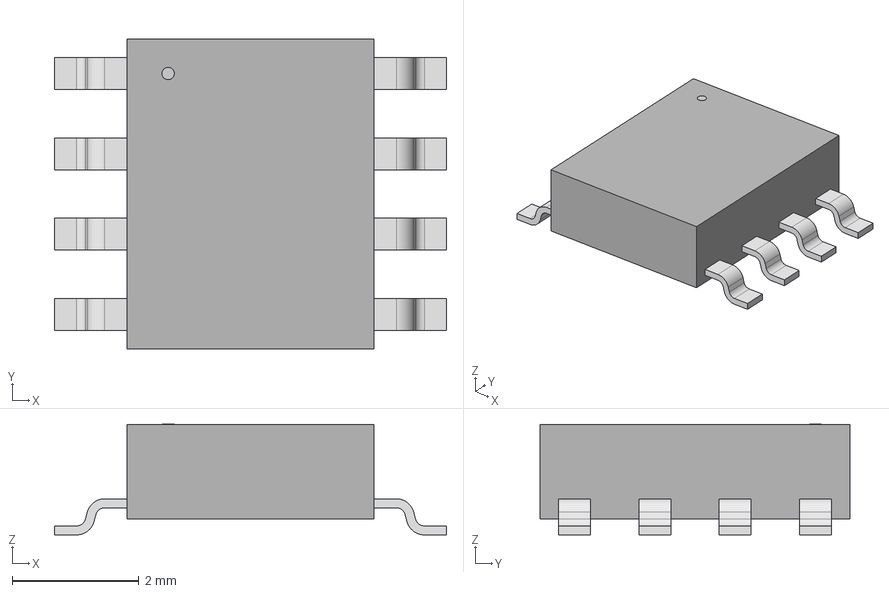
[picture p83: CAD file, 2025-09-09]
3dmodels/SOIC8_4P9X3P9MC_MCH.step
6.20 x 4.90 x 1.75 mm
