AbdulAjadi1/FPGA-Board/3dmodels/C_0805_2012Metric.step

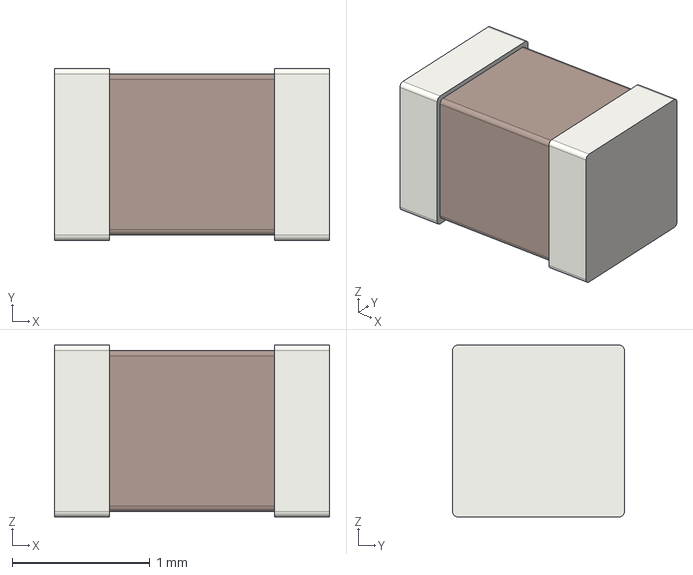
[picture p84: CAD file, 2025-09-09]
3dmodels/C_0805_2012Metric.step
2.00 x 1.25 x 1.25 mm
