AbdulAjadi1/FPGA-Board/3dmodels/MLP6_2X2_ONS.step

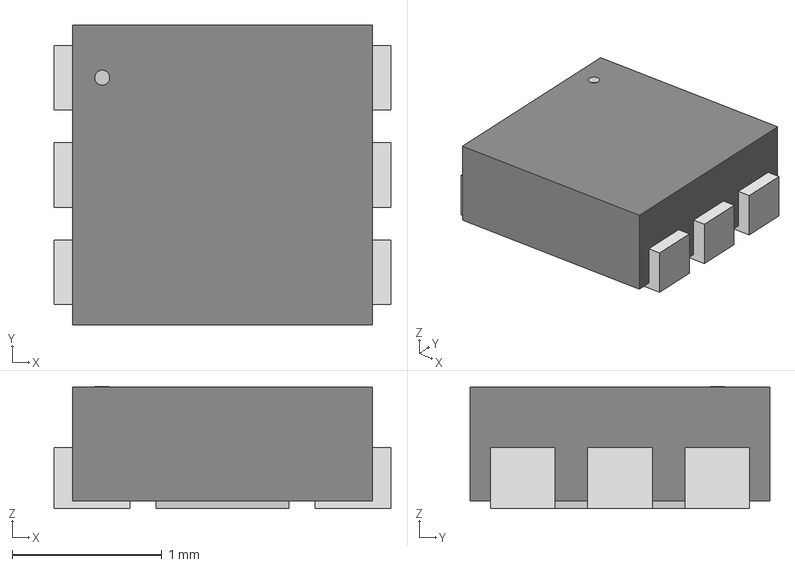
[picture p85: CAD file, 2025-09-09]
3dmodels/MLP6_2X2_ONS.step
2.25 x 2.01 x 0.815 mm
