AbdulAjadi1/FPGA-Board/3dmodels/C_1210_3225Metric.step

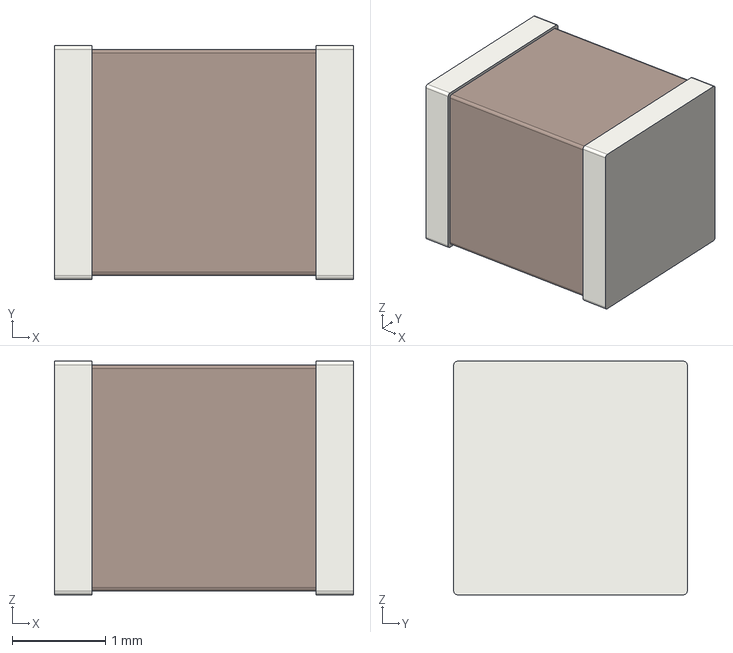
[picture p86: CAD file, 2025-09-09]
3dmodels/C_1210_3225Metric.step
3.20 x 2.50 x 2.50 mm
