AbdulAjadi1/FPGA-Board/3dmodels/T491B157M006AT.STEP

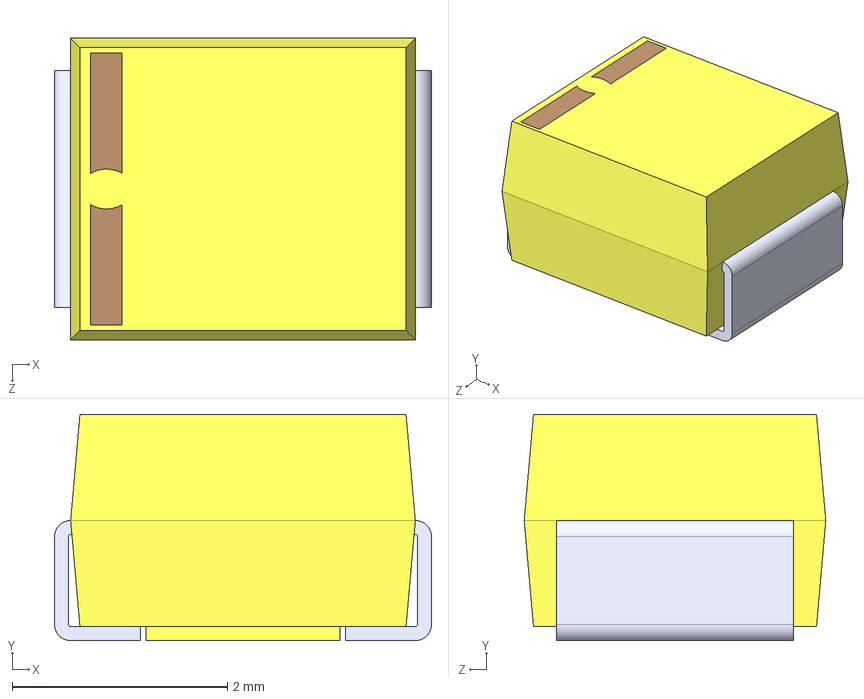
[picture p87: CAD file, 2025-09-09]
3dmodels/T491B157M006AT.STEP
3.50 x 2.10 x 2.80 mm
