AbdulAjadi1/FPGA-Board/3dmodels/PinSocket_1x08_P2.54mm_Vertical.step

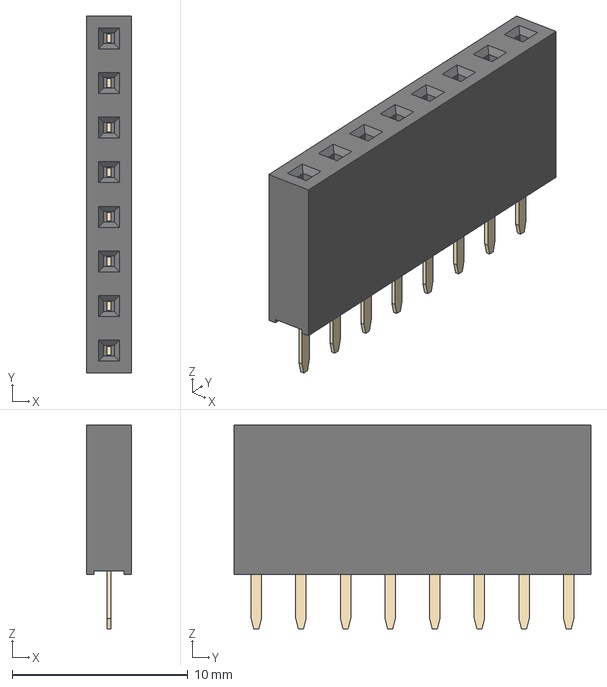
[picture p88: CAD file, 2025-09-09]
3dmodels/PinSocket_1x08_P2.54mm_Vertical.step
2.54 x 20.3 x 11.6 mm
