AbdulAjadi1/FPGA-Board/3dmodels/SC-74A_318BQ_ONS.step

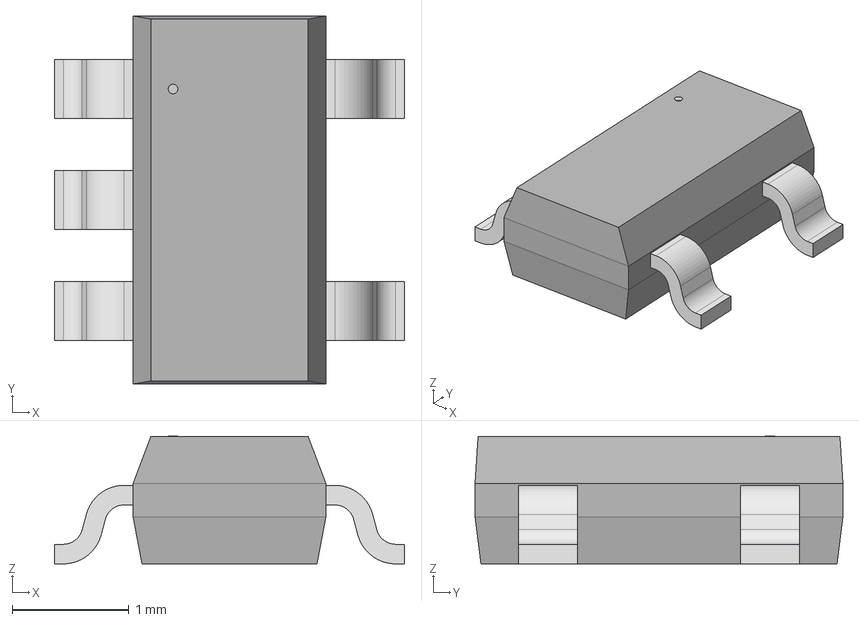
[picture p89: CAD file, 2025-09-09]
3dmodels/SC-74A_318BQ_ONS.step
3.00 x 3.15 x 1.09 mm
