AbdulAjadi1/FPGA-Board/3dmodels/IND_TAIYO_NR5040_TAY.step

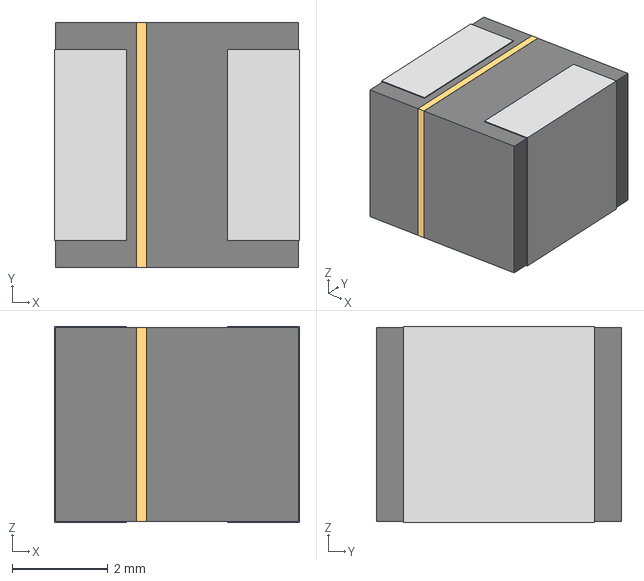
[picture p90: CAD file, 2025-09-09]
3dmodels/IND_TAIYO_NR5040_TAY.step
5.11 x 5.11 x 4.09 mm
