AbdulAjadi1/FPGA-Board/3dmodels/TOTX1950A_F_.stp

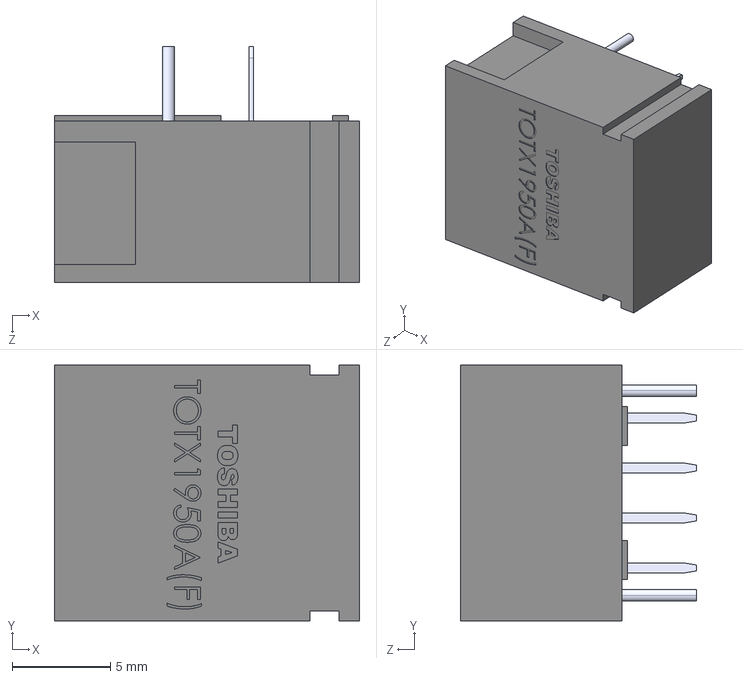
[picture p91: CAD file, 2025-09-09]
3dmodels/TOTX1950A_F_.stp
15.5 x 13.0 x 12.0 mm
