AbdulAjadi1/FPGA-Board/3dmodels/TPD4E05U06DQAR.step

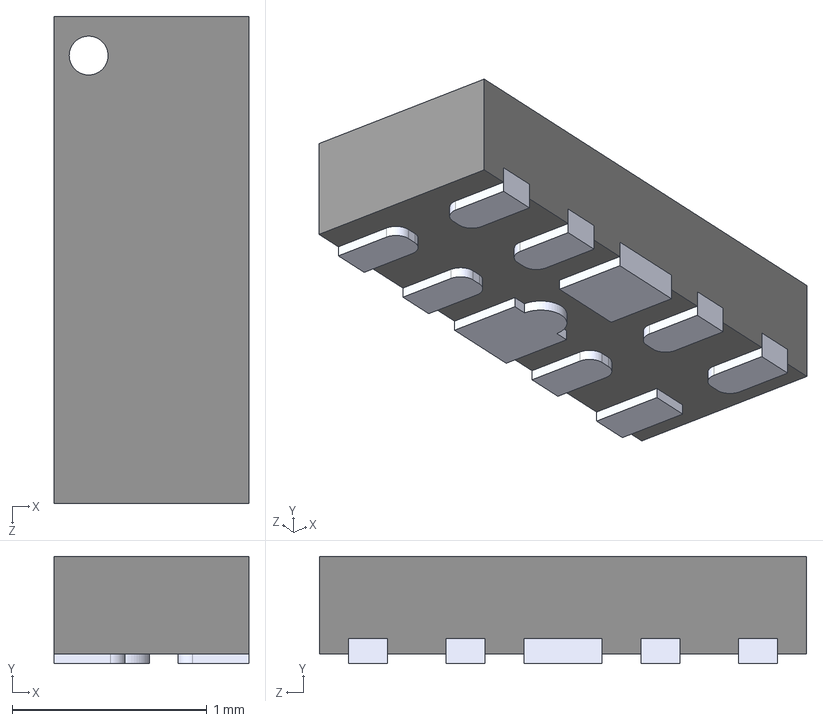
[picture p93: CAD file, 2025-09-09]
3dmodels/TPD4E05U06DQAR.step
1.00 x 0.55 x 2.50 mm
