AbdulAjadi1/FPGA-Board/3dmodels/PPPC062LJBN-RC.STEP

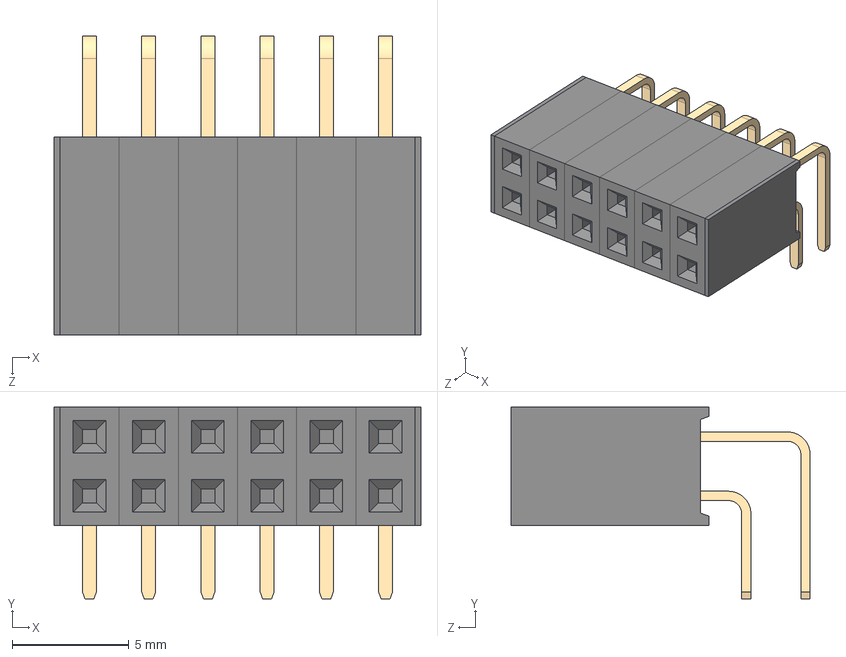
[picture p94: CAD file, 2025-09-09]
3dmodels/PPPC062LJBN-RC.STEP
15.7 x 8.23 x 12.8 mm
PPPC022LJBN-RC_C06
Pin - Gold x 6
