AbdulAjadi1/FPGA-Board/3dmodels/RTL8211F-CG_RTK.step

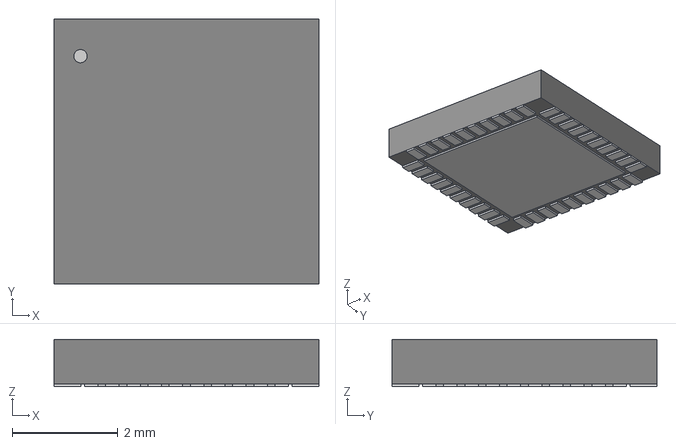
[picture p95: CAD file, 2025-09-09]
3dmodels/RTL8211F-CG_RTK.step
5.00 x 5.00 x 0.892 mm
