AbdulAjadi1/FPGA-Board/3dmodels/BEADC1608X95N.step

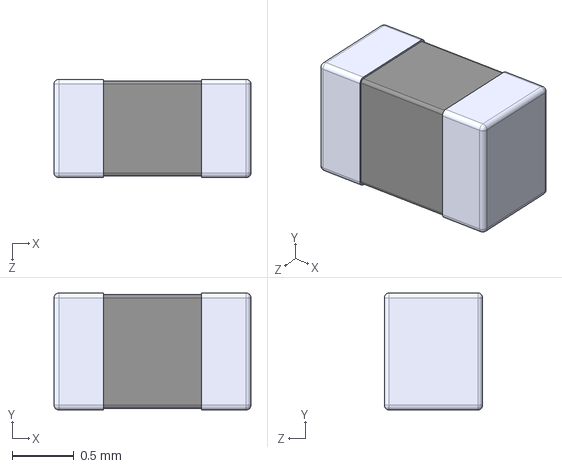
[picture p96: CAD file, 2025-03-25]
3dmodels/BEADC1608X95N.step
1.60 x 0.95 x 0.8 mm
