AbdulAjadi1/FPGA-Board/3dmodels/FDV301N.step

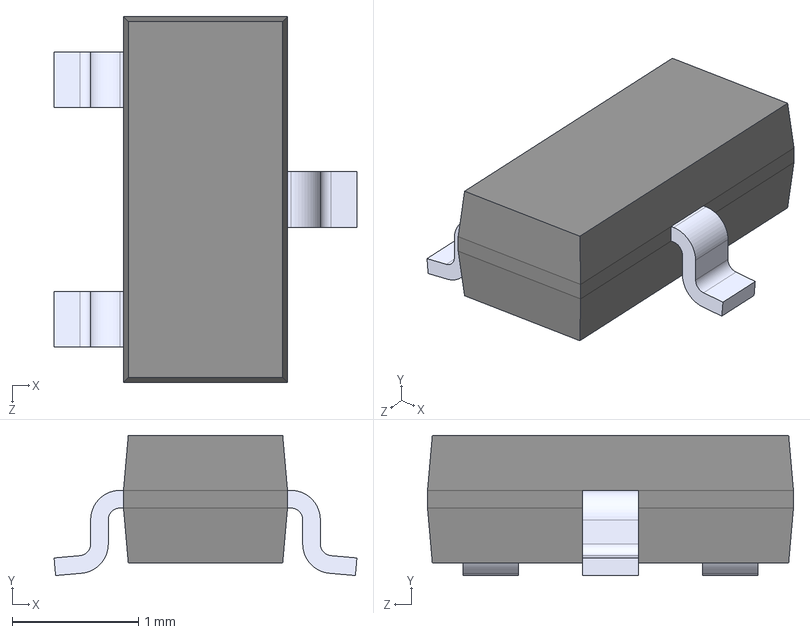
[picture p97: CAD file, 2025-03-25]
3dmodels/FDV301N.step
2.40 x 1.11 x 2.90 mm
