AbdulAjadi1/FPGA-Board/3dmodels/MBT3904DW1T1G.step

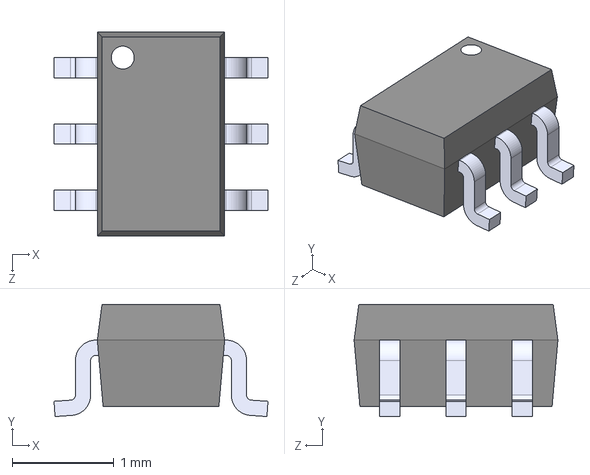
[picture p98: CAD file, 2025-03-25]
3dmodels/MBT3904DW1T1G.step
2.10 x 1.10 x 2.00 mm
